matt-nel/UJ_Fluidic_backbone/CAD_files/syringe_pump/carriage.SLDPRT

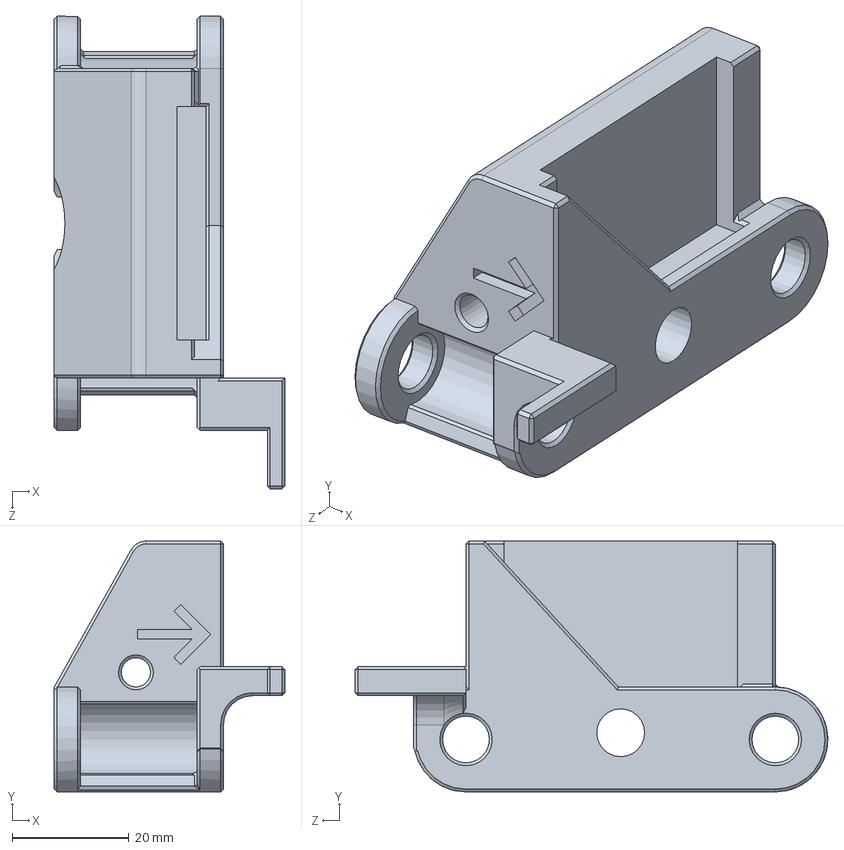
[picture p25: CAD file, 2021-12-11]
CAD_files/syringe_pump/carriage.SLDPRT
39.5 x 43.0 x 81.0 mm
