matt-nel/UJ_Fluidic_backbone/CAD_files/selector_valve/valve_gearbox_mount.SLDPRT

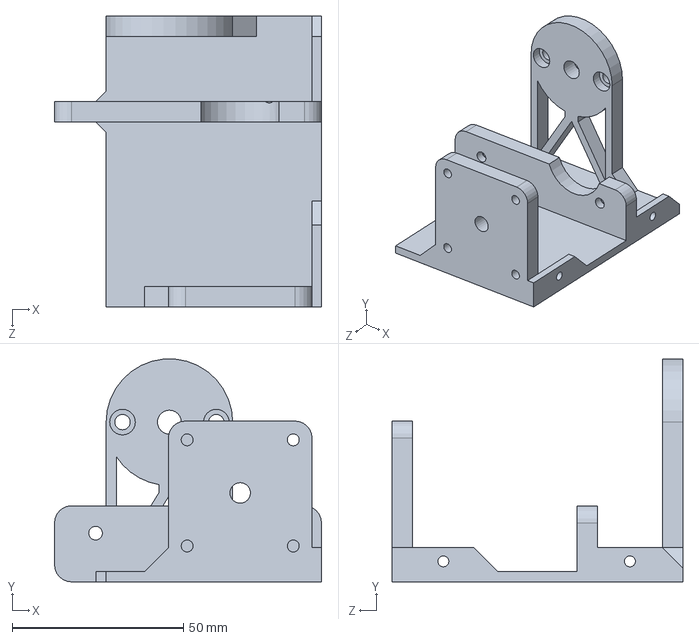
[picture p26: CAD file, 2021-12-11]
CAD_files/selector_valve/valve_gearbox_mount.SLDPRT
78.0 x 65.1 x 85.0 mm
