matt-nel/UJ_Fluidic_backbone/CAD_files/selector_valve/6mm rod.SLDPRT

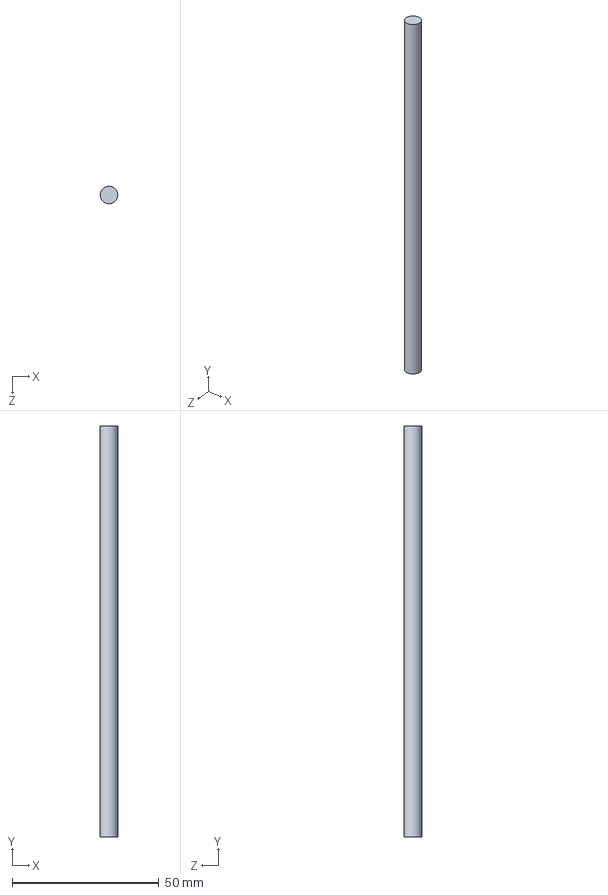
[picture p28: CAD file, 2021-12-11]
CAD_files/selector_valve/6mm rod.SLDPRT
6.00 x 140.0 x 6.00 mm
