matt-nel/UJ_Fluidic_backbone/CAD_files/syringe_pump/gap_sensor.SLDPRT

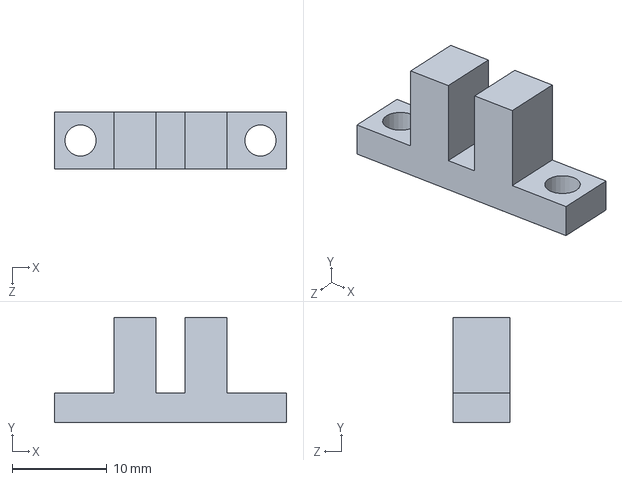
[picture p29: CAD file, 2021-12-11]
CAD_files/syringe_pump/gap_sensor.SLDPRT
24.5 x 11.1 x 6.00 mm
