matt-nel/UJ_Fluidic_backbone/CAD_files/reactor/reactor stand with fan.SLDPRT

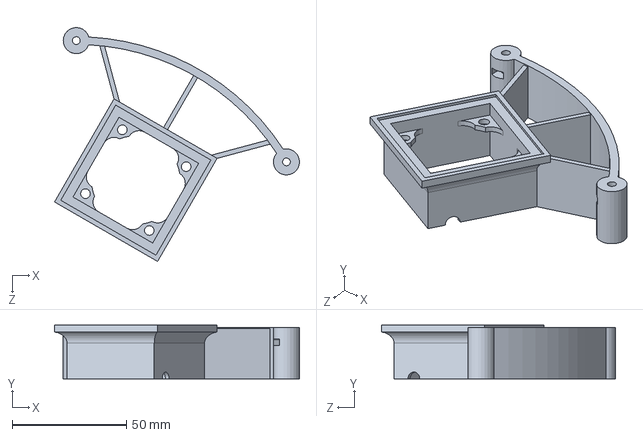
[picture p30: CAD file, 2021-12-11]
CAD_files/reactor/reactor stand with fan.SLDPRT
107.0 x 23.5 x 102.2 mm
