matt-nel/UJ_Fluidic_backbone/CAD_files/syringe_pump/endstop.SLDPRT

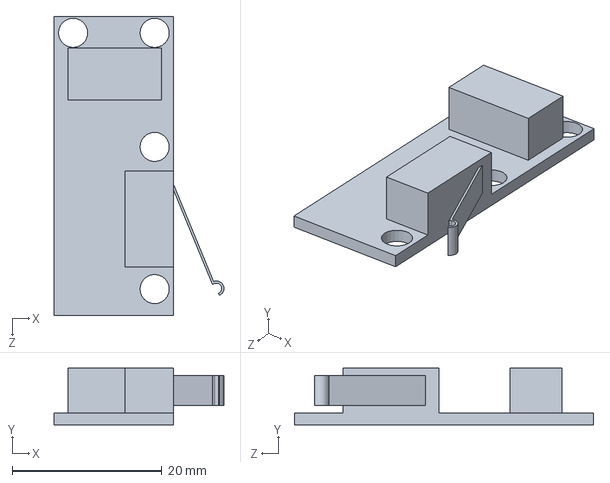
[picture p31: CAD file, 2021-12-11]
CAD_files/syringe_pump/endstop.SLDPRT
22.7 x 7.60 x 40.0 mm
