matt-nel/UJ_Fluidic_backbone/CAD_files/selector_valve/bearing.SLDPRT

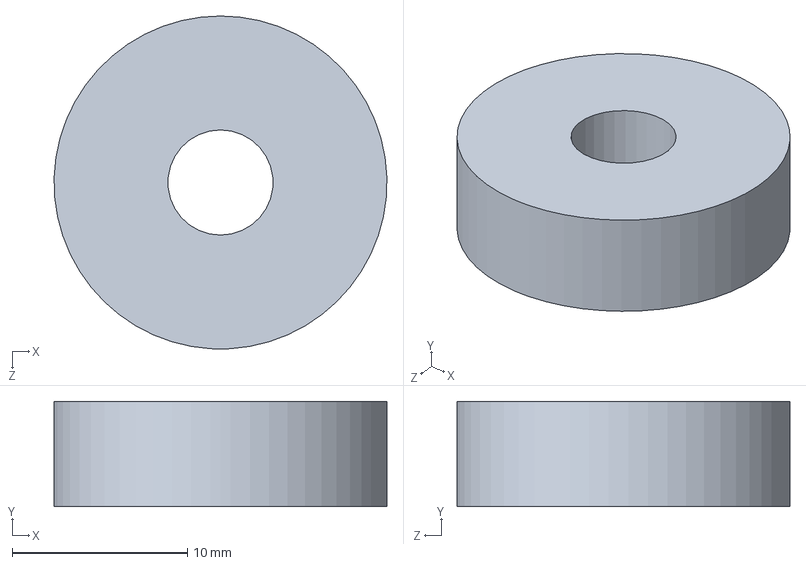
[picture p32: CAD file, 2021-12-11]
CAD_files/selector_valve/bearing.SLDPRT
19.0 x 6.00 x 19.0 mm
