matt-nel/UJ_Fluidic_backbone/CAD_files/syringe_pump/bottom adapter plate.SLDPRT

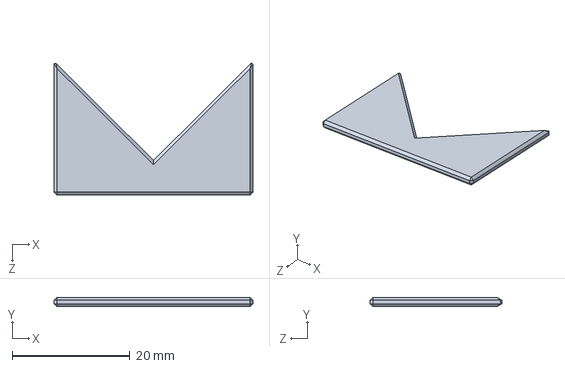
[picture p33: CAD file, 2021-12-11]
CAD_files/syringe_pump/bottom adapter plate.SLDPRT
33.8 x 1.60 x 22.5 mm
