matt-nel/UJ_Fluidic_backbone/CAD_files/reactor/n42 rect magnet.SLDPRT

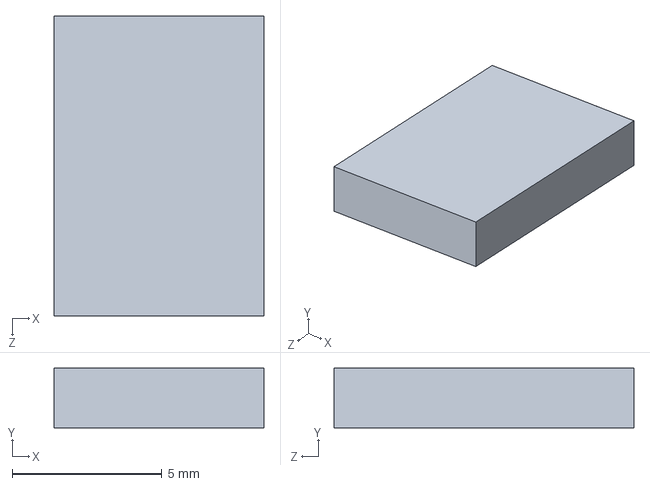
[picture p34: CAD file, 2021-12-11]
CAD_files/reactor/n42 rect magnet.SLDPRT
7.00 x 2.00 x 10.0 mm
