matt-nel/UJ_Fluidic_backbone/CAD_files/selector_valve/Driven gear 26T.SLDPRT

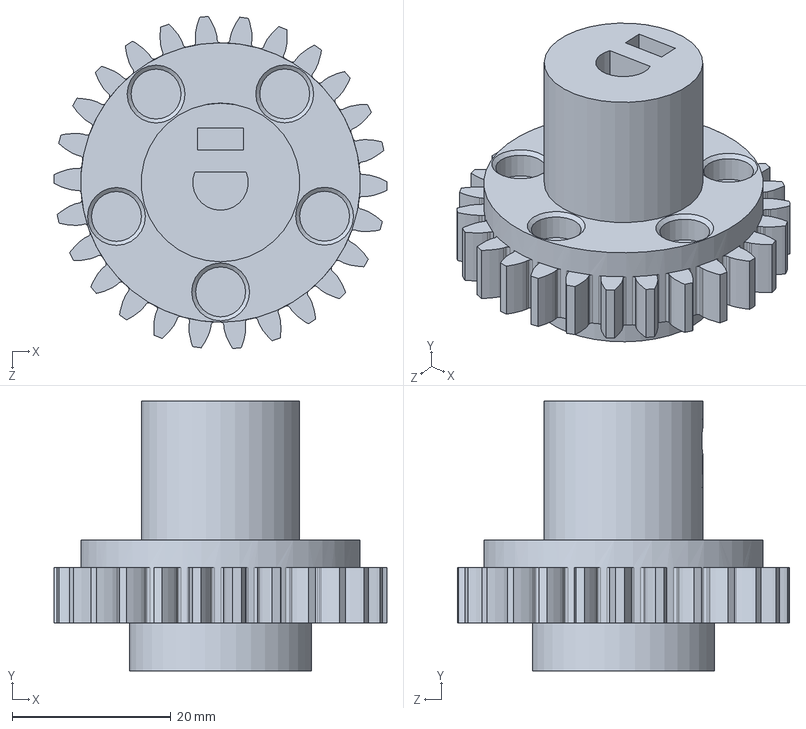
[picture p35: CAD file, 2021-12-11]
CAD_files/selector_valve/Driven gear 26T.SLDPRT
42.0 x 34.0 x 41.9 mm
