matt-nel/UJ_Fluidic_backbone/CAD_files/syringe_pump/carriage_v2.SLDPRT

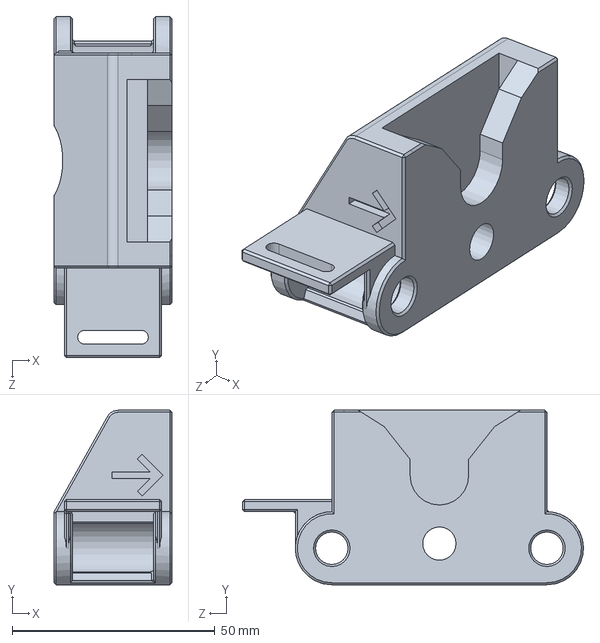
[picture p36: CAD file, 2021-12-11]
CAD_files/syringe_pump/carriage_v2.SLDPRT
29.0 x 43.0 x 84.0 mm
