matt-nel/UJ_Fluidic_backbone/CAD_files/selector_valve/grub.SLDPRT

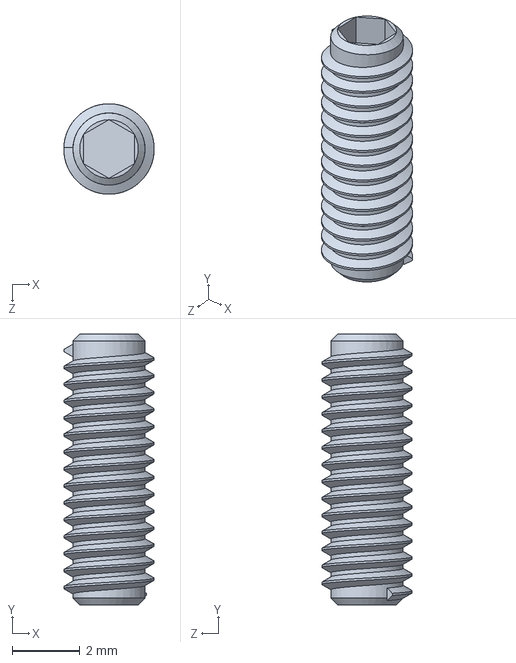
[picture p37: CAD file, 2021-12-11]
CAD_files/selector_valve/grub.SLDPRT
2.67 x 8.00 x 2.67 mm
