matt-nel/UJ_Fluidic_backbone/CAD_files/selector_valve/valve_gearbox_mount_vici.SLDPRT

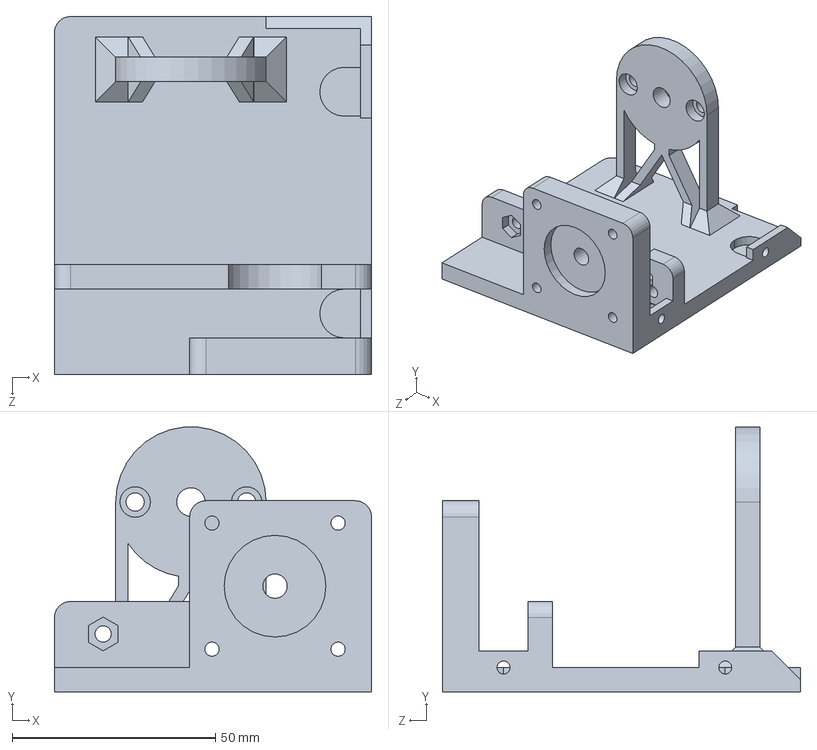
[picture p38: CAD file, 2021-12-11]
CAD_files/selector_valve/valve_gearbox_mount_vici.SLDPRT
78.0 x 65.1 x 88.0 mm
