matt-nel/UJ_Fluidic_backbone/CAD_files/syringe_pump/LM6UU.SLDPRT

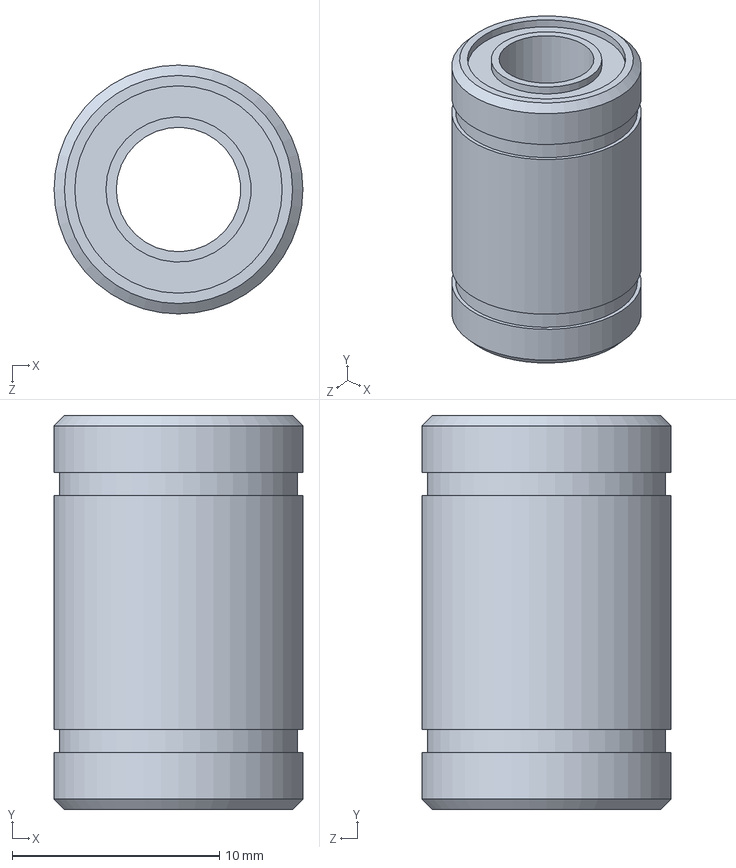
[picture p39: CAD file, 2021-12-11]
CAD_files/syringe_pump/LM6UU.SLDPRT
12.0 x 19.0 x 12.0 mm
