matt-nel/UJ_Fluidic_backbone/CAD_files/syringe_pump/syringe_holder.SLDPRT

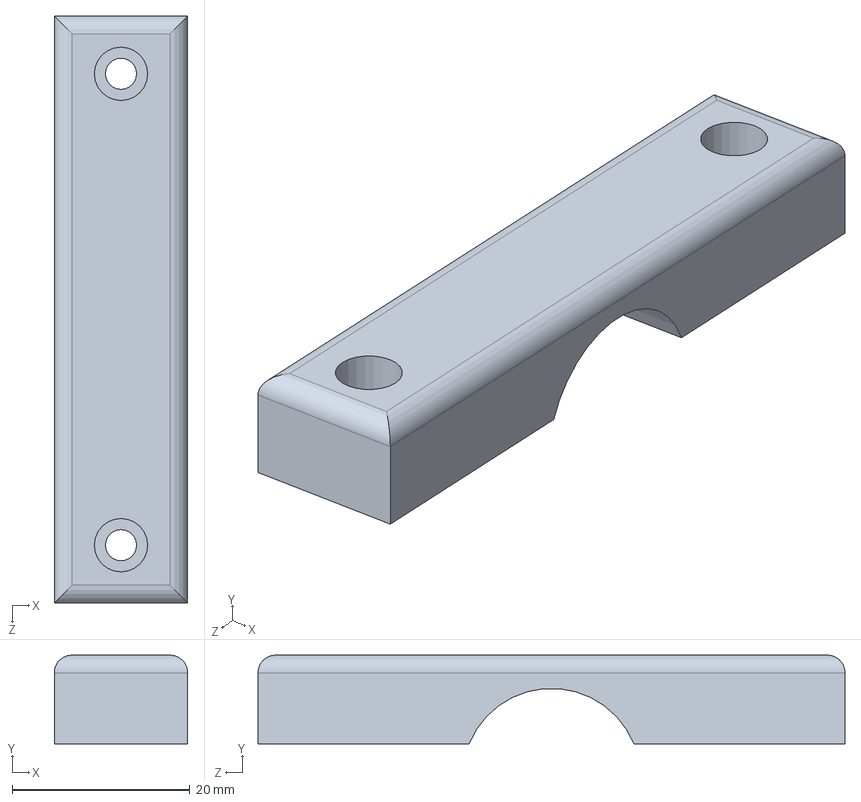
[picture p40: CAD file, 2021-12-11]
CAD_files/syringe_pump/syringe_holder.SLDPRT
15.0 x 10.0 x 66.0 mm
