matt-nel/UJ_Fluidic_backbone/CAD_files/syringe_pump/adjustable_endstop_arm.SLDPRT

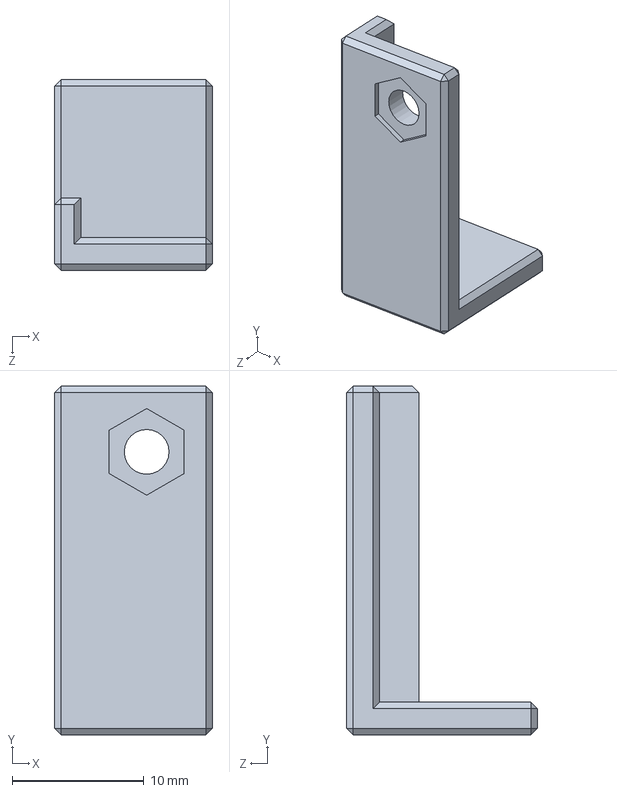
[picture p41: CAD file, 2021-12-11]
CAD_files/syringe_pump/adjustable_endstop_arm.SLDPRT
12.0 x 26.5 x 14.5 mm
