matt-nel/UJ_Fluidic_backbone/CAD_files/selector_valve/Driver gear 13T.SLDPRT

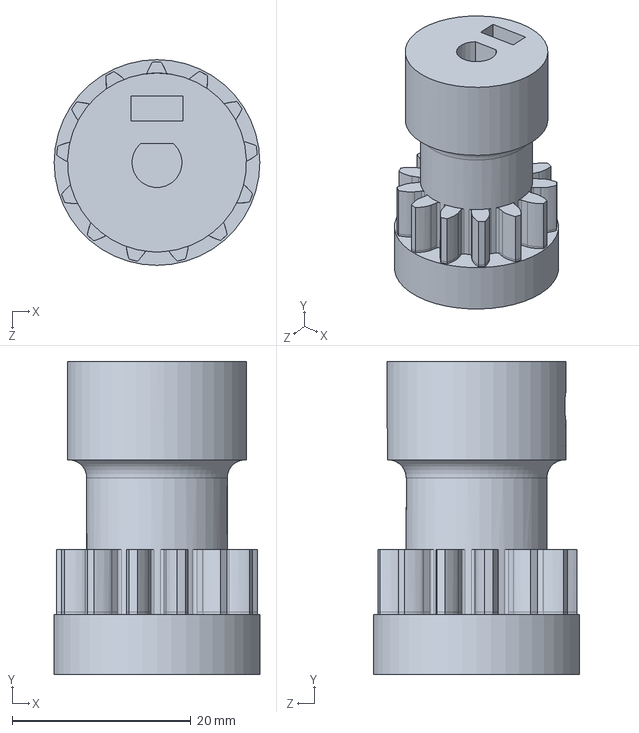
[picture p42: CAD file, 2021-12-11]
CAD_files/selector_valve/Driver gear 13T.SLDPRT
23.0 x 35.0 x 23.0 mm
