matt-nel/UJ_Fluidic_backbone/CAD_files/syringe_pump/slotted_wheel.SLDPRT

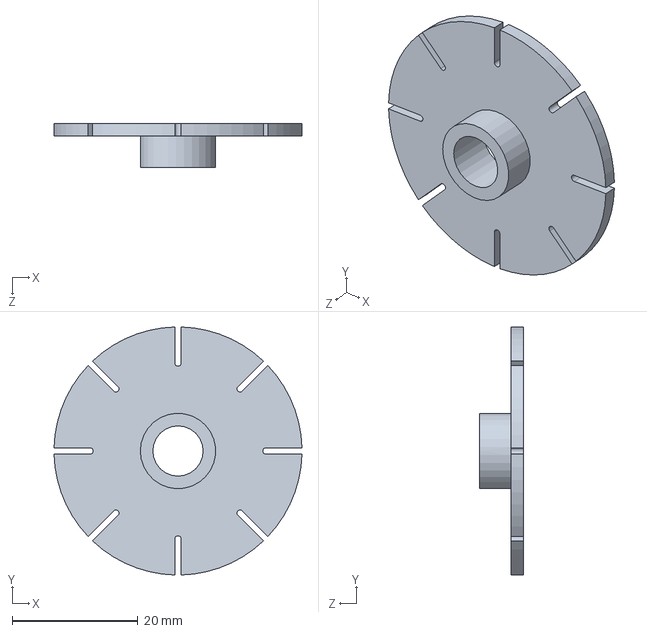
[picture p43: CAD file, 2021-12-11]
CAD_files/syringe_pump/slotted_wheel.SLDPRT
39.5 x 39.5 x 7.00 mm
