matt-nel/UJ_Fluidic_backbone/CAD_files/syringe_pump/endstop arm.SLDPRT

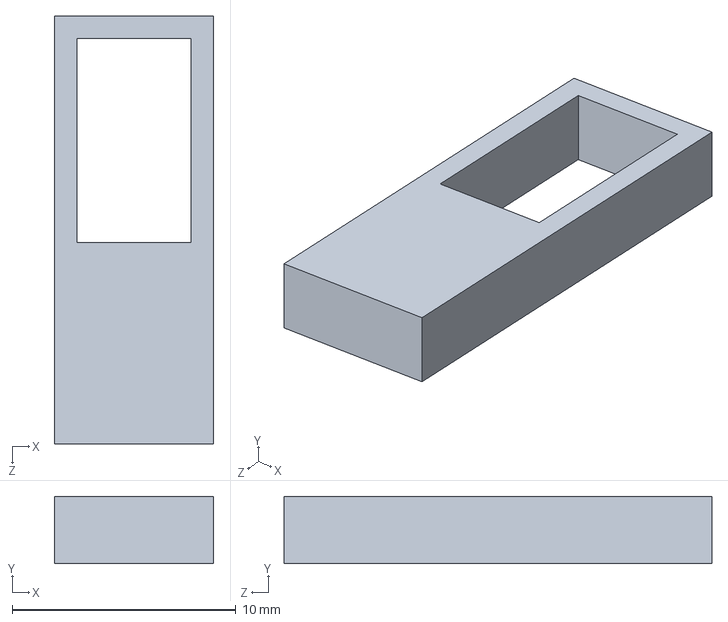
[picture p44: CAD file, 2021-12-11]
CAD_files/syringe_pump/endstop arm.SLDPRT
7.10 x 3.00 x 19.1 mm
