matt-nel/UJ_Fluidic_backbone/CAD_files/syringe_pump/Nema 17 Stepper Motor.SLDPRT

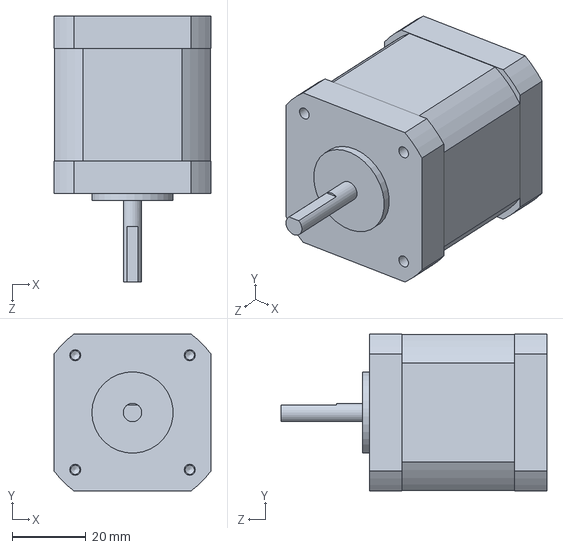
[picture p45: CAD file, 2021-12-11]
CAD_files/syringe_pump/Nema 17 Stepper Motor.SLDPRT
42.4 x 42.4 x 72.0 mm
