matt-nel/UJ_Fluidic_backbone/CAD_files/syringe_pump/syringe_adapter_bottom.SLDPRT

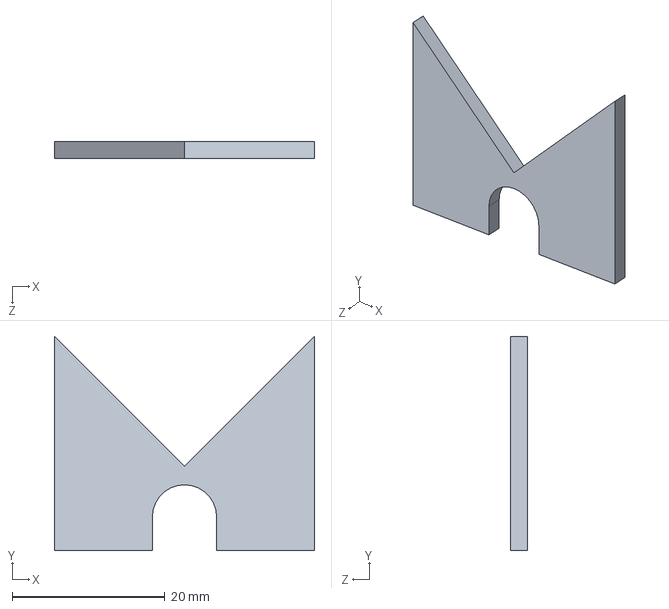
[picture p46: CAD file, 2021-12-11]
CAD_files/syringe_pump/syringe_adapter_bottom.SLDPRT
34.0 x 28.0 x 2.20 mm
