matt-nel/UJ_Fluidic_backbone/CAD_files/selector_valve/M4 x 35.SLDPRT

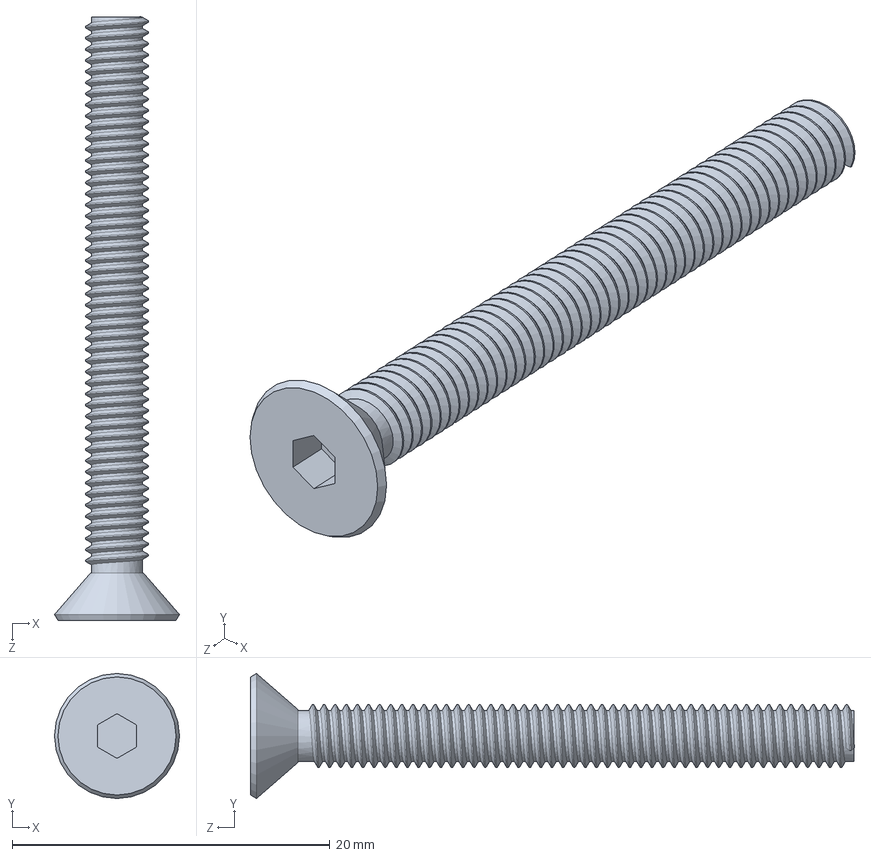
[picture p47: CAD file, 2021-12-11]
CAD_files/selector_valve/M4 x 35.SLDPRT
7.87 x 7.87 x 38.0 mm
