matt-nel/UJ_Fluidic_backbone/CAD_files/syringe_pump/tr8x8 115 mm.SLDPRT

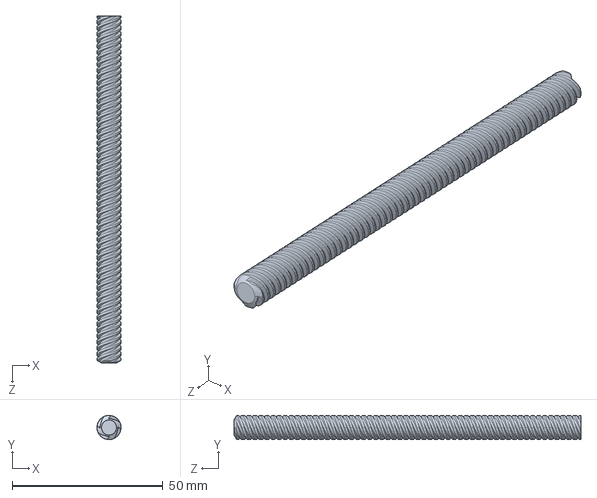
[picture p48: CAD file, 2021-12-11]
CAD_files/syringe_pump/tr8x8 115 mm.SLDPRT
8.00 x 8.00 x 115.0 mm
