matt-nel/UJ_Fluidic_backbone/CAD_files/selector_valve/8-32-8.SLDPRT

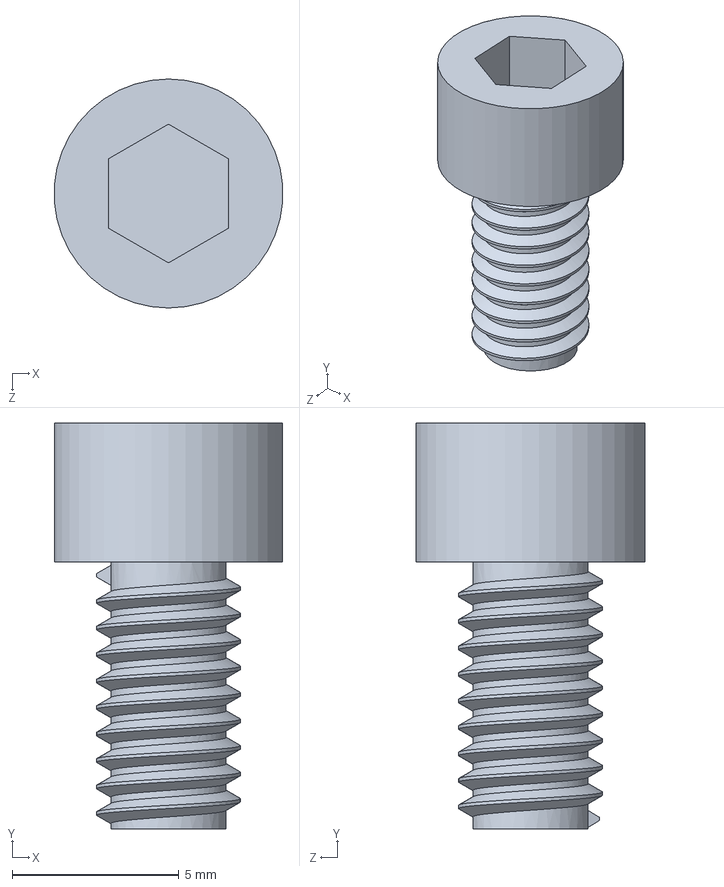
[picture p49: CAD file, 2021-12-11]
CAD_files/selector_valve/8-32-8.SLDPRT
6.84 x 12.2 x 6.86 mm
