matt-nel/UJ_Fluidic_backbone/CAD_files/selector_valve/Driven gear 25T.SLDPRT

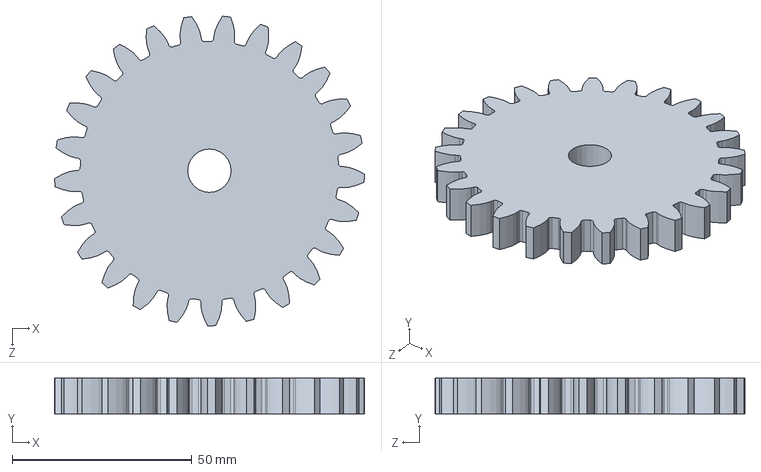
[picture p50: CAD file, 2021-12-11]
CAD_files/selector_valve/Driven gear 25T.SLDPRT
86.3 x 10.0 x 86.2 mm
