matt-nel/UJ_Fluidic_backbone/CAD_files/syringe_pump/adapter plate.SLDPRT

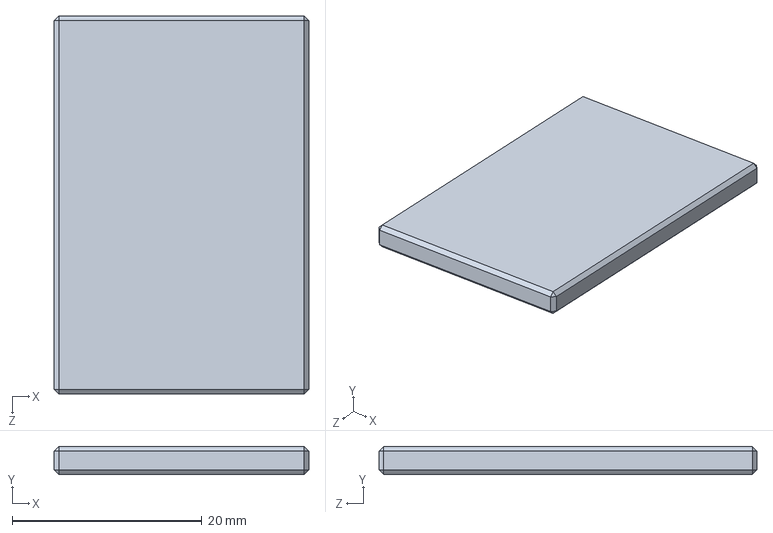
[picture p51: CAD file, 2021-12-11]
CAD_files/syringe_pump/adapter plate.SLDPRT
26.8 x 3.00 x 39.8 mm
