matt-nel/UJ_Fluidic_backbone/CAD_files/syringe_pump/Flexible Coupling 5mm x 8mm.SLDPRT

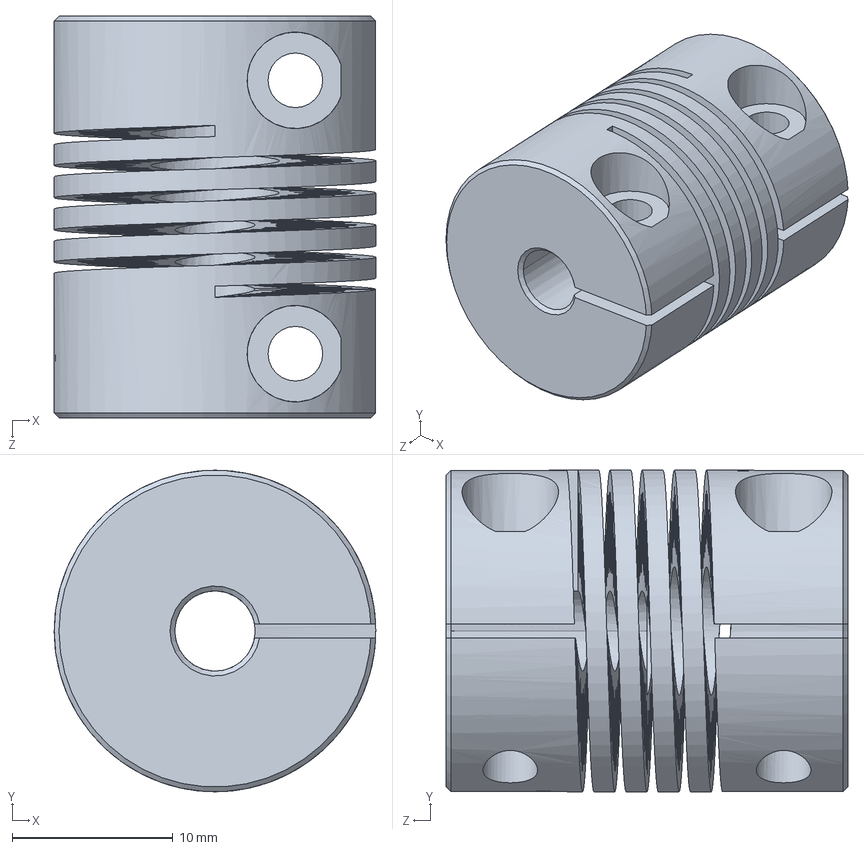
[picture p52: CAD file, 2021-12-11]
CAD_files/syringe_pump/Flexible Coupling 5mm x 8mm.SLDPRT
20.0 x 20.0 x 25.0 mm
