matt-nel/UJ_Fluidic_backbone/robot_setup.py

"""
 This script is used to start the setup program. The setup program will create the
 JSON files necessary to run the robot within the folder where the package has been
 installed on your system. 
"""

from UJ_FB import robot_setup

robot_setup()
