matt-nel/UJ_Fluidic_backbone/src/UJ_FB/setup_GUI.py

"""
This script contains the classes used to create JSON configuration files for the robot. 
Using this the SetupGUI, users can configure the robots graphically, without writing
JSON. This GUI assumes that the robot is run using an Arduino Mega 2560 and a RAMPS 1.4 
board. Most of the configuration information is temporarily held as a networkx graph. 
When the user generates the configuration files, the graph is encoded as a JSON file 
detailed the nodes and links (edges) of the graph. 
"""


import UJ_FB
import tkinter as tk
import os
import sys
import subprocess
import serial.tools.list_ports
import json
from PIL import ImageTk, Image
import cv2 as cv
import numpy as np
import networkx as nx

FIELD_NAMES = {"Maximum volume in ml": "max_volume",
               "Current volume in ml": "cur_volume",
               "Aluminium volume [m3] (eg. 1e-6)": "aluminium_volume",
               "Name": "name",
               "Fan speed RPM": "fan_speed",
               "Maximum samples": "max_samples",
               "Contents": "contents"
               }

UNITS = {"max_volume": "float",
         "cur_volume": "float",
         "fan_speed": "int",
         "max_samples": "int"}


def start_gui():
    root = tk.Tk()
    SetupGUI(root)
    root.mainloop()


def populate_ports():
    """
    Gets the serial ports available for connection
    :return: List of Arduinos available on the system
    """
    if sys.platform.startswith("win"):
        arduino_list = [port for port in serial.tools.list_ports.comports() if "arduino" in port.description.lower()]
    elif sys.platform.startswith("linux") or sys.platform.startswith("cygwin"):
        arduino_list = [port for port in serial.tools.list_ports.comports() if "acm" in port.description.lower()]
    else:
        raise EnvironmentError("Unsupported platform")

    return [name.name for name in arduino_list]


class CmdConfig:
    """Simple class to hold and generate the configuration for the CommandManager.
    """
    def __init__(self):
        self.ios = []
        self.devices = {}

    def load_existing(self, ios, devices):
        self.ios = ios
        self.devices = devices

    def as_dict(self):
        return {"ios": self.ios, "devices": self.devices}


class SetupGUI:
    """Class used to run the GUI. 
    """
    def __init__(self, primary):
        # Setup initialisation
        self.primary = primary
        self.primary.title("Fluidic backbone setup")
        self.primary.configure(background="#FFFFFF")

        script_dir = os.path.abspath(UJ_FB.__file__)
        script_dir = script_dir.split("\\")
        self.script_dir = "\\".join(script_dir[:-1])
        if not os.path.exists(os.path.join(self.script_dir, "configs")):
            os.chdir(self.script_dir)
            os.mkdir("configs")
        self.config_filenames = ["cmd_config.json", "module_connections.json", "running_config.json"]
        self.default_configs = ["default_configs/single_valve/", "default_configs/single_valve_reactor/",
                                "default_configs/two_valve_reactor/", "configs/"]

        self.frame = np.array([])
        self.fonts = {"buttons": ("Comic Sans MS", 12), "labels": ("Comic Sans MS", 14),
                      "default": ("Comic Sans MS", 16),
                      "heading": ("Comic Sans MS", 16), "text": ("Comic Sans MS", 12)}
        self.colours = {"accept-button": "#4de60b", "cancel-button": "#e6250b",
                        "heading": "#e65525", "other-button": "#45296e", "other-button-text": "#FFFFFF",
                        "form-bg": "#b5d5ff", "form-bg2": "#377bd4"}
        image_dir = os.path.join(self.script_dir, "valve.png")
        self.valve_image = ImageTk.PhotoImage(Image.open(image_dir))
        self.text_temp = ""
        self.int_temp = 0
        self.config_cmd_flag = False
        self.config_cxn_flag = False
        self.exit_flag = False

        # Robot parameters
        self.key = ""
        self.id = ""
        self.rxn_name = ""
        self.roi = []
        self.used_motor_connectors = {}
        self.used_endstop_connectors = {}
        self.used_he_pins = []
        self.used_valves = []
        self.com_ports = []

        self.modules = {}
        self.graph = nx.MultiGraph()
        self.graph_tmp = nx.MultiGraph()
        self.node_config = None
        self.num_syringes = 0
        self.num_valves = 0
        self.conf_syr = 0
        self.conf_valves = 0
        self.conf_storage = 0
        self.num_he_sens = 0
        self.num_flasks = 0
        self.num_reactors = 0
        self.valves_buttons = {}
        self.simulation = False
        self.cmd_devices = CmdConfig()
        self.default_running_config = {
            "url": "http://127.0.0.1:5000/robots_api",
            "magnet_readings": {"valve1": {"1": 0, "3": 0, "5": 0, "7": 0, "9": 0}, "valve2": {"1": 0, "3": 0,
                                                                                               "5": 0, "7": 0, "9": 0},
                                "check_magnets": 0},
            "valve_backlash": {"valve1": {"check_backlash": 0, "backlash_steps": 0},
                               "valve2": {"check_backlash": 0, "backlash_steps": 0}},
            "valve_pos": {"valve1": None, "valve2": None}}

        self.es_options = {"X min": 3, "X max": 2, "Y min": 14, "Y max": 15, "Z min": 18, "Z max": 19}
        self.motor_configs = {"default": {"steps_per_rev": 3200, "enabled_acceleration": False, "speed": 1000,
                                          "max_speed": 10000, "acceleration": 1000},
                              "cmd_default": {"enabled_acceleration": False, "speed": 1000, "max_speed": 10000,
                                              "acceleration": 1000},
                              "valve": {"steps_per_rev": 3200, "enabled_acceleration": False, "speed": 1000,
                                        "max_speed": 4000, "acceleration": 1000}
                              }
        self.motor_options = {"X": {"stepperX": {"cmd_id": "STPX",
                                                 "device_config": {}}},
                              "Y": {"stepperY": {"cmd_id": "STPY",
                                                 "device_config": {}}},
                              "Z": {"stepperZ": {"cmd_id": "STPZ",
                                                 "device_config": {}}},
                              "E0": {"stepperE0": {"cmd_id": "STPE0",
                                                   "device_config": {}}},
                              "E1": {"stepperE1": {"cmd_id": "STPE1",
                                                   "device_config": {}}}}

        steppers = [("stepperX", "STPX"), ("stepperY", "STPY"), ("stepperZ", "STPZ"),
                    ("stepperE0", "STPE0"), ("stepperE1", "STPE1")]
        for stepper in steppers:
            self.cmd_devices.devices[stepper[0]] = {"command_id": stepper[1],
                                                    "config": self.motor_configs["default"]}

        # Setup UI
        self.setup_frame = tk.Frame(self.primary, bg=self.colours["form-bg"], borderwidth=5)
        self.utilities_frame = tk.Frame(self.primary, bg=self.colours["form-bg"], borderwidth=2, height=40)
        self.log_frame = tk.Frame(self.primary)
        self.log = tk.Text(self.log_frame, state="disable", width=80, height=8, wrap="none", borderwidth=5)

        self.setup_label = tk.Label(self.primary, text="Fluidic backbone setup:", font=self.fonts["heading"],
                                    fg=self.colours["heading"], bg="#FFFFFF",
                                    padx=2)
        self.utilities_label = tk.Label(self.primary, text="Utilities", font=self.fonts["heading"], padx=2,
                                        bg="#ffffff", fg=self.colours["heading"])

        self.log_frame.grid(row=4, column=2, padx=5, pady=10)
        self.log.grid(row=0, column=0)
        self.setup_label.grid(row=2, column=2)
        self.utilities_label.grid(row=2, column=10)
        self.setup_frame.grid(row=3, column=2)
        self.utilities_frame.grid(row=3, column=10)

        self.init_setup_panel()
        self.init_utilities_panel()

    def init_setup_panel(self):
        """Starts the setup frame, which is the main part of the initial window. Using this frame,
        user can configure the serial port, robot id, robot key, reaction name, and module information.
        """
        def display_ports(ports, refresh=False):
            i = 0
            if ports:
                label = tk.Label(com_frame, text="Available ports:", font=self.fonts["heading"],
                                 bg=self.colours["form-bg"], fg=self.colours["heading"])
                label.grid(row=2, columnspan=2)
                for name in ports:
                    c_port_button = tk.Button(com_frame, text="Arduino on " + name, font=button_font,
                                              bg=self.colours["other-button"],
                                              fg=self.colours["other-button-text"], width=20,
                                              command=lambda: add_com_port(name))
                    c_port_button.grid(row=3, column=i)
                    i += 1
            else:
                ports = populate_ports()
                if ports and refresh:
                    display_ports(ports)
                else:
                    no_ports = tk.Label(com_frame, text="No ports available, click refresh or use the text box",
                                        font=self.fonts["labels"], bg="gray", fg=self.colours["other-button-text"],)
                    no_ports.grid(row=3, column=i)

        def add_com_port(port_name=""):
            if port_name == "":
                port = self.text_temp
                self.cmd_devices.ios.append({"port": port})
                self.write_message(f"Port {port} added")
                com_port_entry.delete(0, "end")
            else:
                if "tty" in port_name:
                    port_name = "/dev/" + port_name
                self.cmd_devices.ios.append({"port": port_name})
                self.write_message(f"Port {port_name} added")

        def add_key():
            self.key = self.text_temp
            robot_key_entry.delete(0, "end")
            self.write_message(f"Robot key added")

        def add_id():
            self.id = self.text_temp
            robot_id_entry.delete(0, "end")
            self.write_message(f"Robot ID added")

        def add_rxn_name():
            self.rxn_name = reaction_name_entry.get()
            reaction_name_entry.delete(0, "end")
            self.write_message(f"Reaction name {self.rxn_name} added")

        button_font = self.fonts["buttons"]
        com_frame = tk.Frame(self.setup_frame, bg=self.colours["form-bg2"], pady=4)
        com_frame.grid(row=2)

        com_port_label = tk.Label(self.setup_frame, text="Choose an arduino to connect to by clicking the button,\n"
                                                         "or write the name of the "
                                                         "com port in the text box and click accept:",
                                  font=self.fonts["labels"], fg=self.colours["heading"], bg=self.colours["form-bg"],)
        com_port_label.grid(row=1, column=0)
        avail_ports = populate_ports()
        refresh_button = tk.Button(com_frame, text="Refresh", font=button_font, bg="LemonChiffon2",
                                   fg="black", command=lambda: display_ports(avail_ports, refresh=True), width=15)
        refresh_button.grid(row=3, column=2)
        display_ports(avail_ports)

        val_text = self.primary.register(self.validate_text)
        cp_entry_label = tk.Label(com_frame, text="Please enter the COM port: ", bg=self.colours["form-bg"],
                                  font=self.fonts["labels"], fg=self.colours["heading"], width=25)
        com_port_entry = tk.Entry(com_frame, validate="key", validatecommand=(val_text, "%P"),
                                  bg="#FFFFFF", fg="black", width=15)
        com_port_button = tk.Button(com_frame, text="Accept port", font=self.fonts["buttons"], bg="lawn green",
                                    fg="black", command=add_com_port, width=15)

        cp_entry_label.grid(row=4, column=0, padx=4)
        com_port_entry.grid(row=4, column=1, padx=4)
        com_port_button.grid(row=4, column=2, padx=4)

        robot_id_label = tk.Label(com_frame, text="Please enter the robot ID: ", bg=self.colours["form-bg"],
                                  font=self.fonts["labels"], fg=self.colours["heading"], width=25)
        robot_id_entry = tk.Entry(com_frame, validate="key", validatecommand=(val_text, "%P"), bg="#FFFFFF", fg="black",
                                  width=15)
        robot_id_button = tk.Button(com_frame, text="Accept ID", font=button_font, bg="lawn green", fg="black",
                                    command=add_id, width=15)

        robot_key_label = tk.Label(com_frame, text="Please enter the robot key: ", font=self.fonts["labels"],
                                   bg=self.colours["form-bg"], fg=self.colours["heading"], width=25)
        robot_key_entry = tk.Entry(com_frame, validate="key", validatecommand=(val_text, "%P"), bg="#FFFFFF",
                                   fg="black", width=15)
        robot_key_button = tk.Button(com_frame, text="Accept key", font=button_font, bg="lawn green", fg="black",
                                     command=add_key, width=15)
        reaction_name_label = tk.Label(com_frame, text="Please enter reaction name: ", font=self.fonts["labels"],
                                       bg=self.colours["form-bg"], fg=self.colours["heading"], width=25)
        reaction_name_butt = tk.Button(com_frame, text="Accept name", font=self.fonts["buttons"],
                                       bg="lawn green", command=add_rxn_name, width=15)
        reaction_name_entry = tk.Entry(com_frame, width=15)

        robot_id_label.grid(row=5, column=0, padx=4)
        robot_id_entry.grid(row=5, column=1, padx=4)
        robot_id_button.grid(row=5, column=2, padx=4)
        robot_key_label.grid(row=6, column=0, padx=4)
        robot_key_entry.grid(row=6, column=1, padx=4)
        robot_key_button.grid(row=6, column=2, padx=4)
        reaction_name_label.grid(row=7, column=0, padx=4)
        reaction_name_entry.grid(row=7, column=1, padx=4)
        reaction_name_butt.grid(row=7, column=2, padx=4)

        mod_frame = tk.Frame(self.setup_frame, bg=self.colours["form-bg"])
        mod_label = tk.Label(mod_frame, text="Backbone modules and connections setup:", font=self.fonts["labels"],
                             bg=self.colours["form-bg"], fg=self.colours["heading"])
        mod_button = tk.Button(mod_frame, text="Configure modules", font=button_font, bg=self.colours["other-button"],
                               fg=self.colours["other-button-text"], command=self.graph_setup, width=20)

        mod_frame.grid(row=3)
        mod_label.grid(row=1, column=0, padx=60)
        mod_button.grid(row=1, column=2, pady=4)

    def init_utilities_panel(self):
        """Contains the buttons used to load existing configuration files, clear the current configuration,
        or start the robot as a subprocess.
        """
        but_width = 25
        button_font = self.fonts["buttons"]
        run_fb_button = tk.Button(self.utilities_frame, text="Run Fluidic Backbone", font=self.fonts["buttons"],
                                  bg="DeepSkyBlue", fg="black", command=self.run_fb_menu, width=but_width, padx=2)
        lc_butt = tk.Button(self.utilities_frame, text="Load existing configuration", font=button_font,
                            bg=self.colours["other-button"], fg=self.colours["other-button-text"],
                            command=self.load_configs, width=but_width, padx=2)
        cc_butt = tk.Button(self.utilities_frame, text="Clear configuration", font=self.fonts["buttons"],
                            bg="Tomato2", fg="black", command=self.clear_configs, width=but_width, padx=2)
        dc_butt = tk.Button(self.utilities_frame, text="Load a default configuration", font=self.fonts["buttons"],
                            bg=self.colours["other-button"], fg=self.colours["other-button-text"],
                            command=self.load_default_config, width=but_width, padx=2)
        gen_button = tk.Button(self.utilities_frame, text="Save configuration", font=button_font, bg="lawn green",
                               fg="black", command=self.generate_config, width=but_width, padx=2)

        lc_butt.grid(row=1, column=0, padx=4, pady=4)
        dc_butt.grid(row=2, column=0, padx=4, pady=4)
        gen_button.grid(row=3, padx=4, pady=4)
        cc_butt.grid(row=4, column=0, padx=4, pady=4)
        run_fb_button.grid(row=5, column=0, padx=4, pady=10)

    def graph_setup(self):
        """This function is used to set up the graph for the robot. The networkx graph contains all the information 
        required by the Fluidic Backbone to set up and control the modules. 
        """
        def accept():
            if self.conf_valves > 0 and self.conf_syr > 0:
                self.config_cxn_flags = True
                self.config_cmd_flag = True
                self.graph = self.graph_tmp
                graph_setup.destroy()
            else:
                self.write_message("Required to configure at least one valve and syringe")

        def reset_graph_setup():
            self.modules = {}
            graph_setup.destroy()

        def populate_menus(frame, valve_no, row_count, port, col, pad=2, span=False):
            """Populates the buttons and option menus that surround each valve. Creates a frame to house
            each button and menu.

            Args:
                frame (tk.Frame): the frame that this button is a child of
                valve_no (int): the number of the valve this module is being configured for.
                row_count (int): the current row number to align the frame to 
                port (int): the valve port connected to this module
                col (int): the column to align the frame to
                pad (int, optional): the amount of padding around the frame. Defaults to 2.
                span (bool, optional): whether the frame should span 2. Defaults to False.
            """
            new_frame = tk.Frame(frame)
            col_span = 1
            if span:
                col_span = 2
            row = row_count * 2
            new_frame.grid(row=row, column=col, columnspan=col_span, pady=pad)
            module_type = tk.StringVar(new_frame)
            module_type.set("")
            port_button = tk.Button(new_frame, text=f"Configure port {port}", bg="LightBlue3", fg="black", width=15,
                                    font=self.fonts["buttons"])
            port_button.grid(row=1, column=1)
            port_om = tk.OptionMenu(new_frame, module_type, *module_options)
            port_om.grid(row=2, column=1)
            port_button.configure(command=lambda v=valve_no,
                                  mt=module_type, p=port, pb=port_button: port_menu_start(v, mt, p, pb))
            self.valves_buttons[valve_name][port] = port_button
            node = self.get_node(valve_name, port)
            if node:
                port_button.configure(bg="lawn green")
                module_type.set(self.graph_tmp.nodes[node]["mod_type"])

        def port_menu_start(valve_no, module_type, port_no, button):
            """Starts the popup window to configure the module attached to that port. Modules can be reconfigured
            later by clicking on the button again.

            Args:
                valve_no (int): the number of the valve that this module is connected to.
                module_type (tk.StringVar): what type of module is connected to this port.
                port_no (int): the port number (1-10) that this module is connected to
                button (tk.Button): the button used to start this menu
            """
            this_module_type = module_type.get()
            if this_module_type != "":
                port_options_window = tk.Toplevel(self.primary)
                this_valve_name = f"valve{valve_no + 1}"
                # Hold the information about this valve
                valve_info = {"valve_name": this_valve_name, "valve_id": valve_no, "port_no": port_no}
                # Hold known information about the node, used to configure a node on the graph within the 
                # popup window.
                node_info = {"entries": []}
                title = tk.Label(port_options_window, text=f"Configure port {port_no} on {this_valve_name}",
                                 font=self.fonts["heading"], fg=self.colours["heading"])
                title.grid(row=0, column=0, columnspan=2)
                type_label = tk.Label(port_options_window, text=this_module_type.capitalize(),
                                      font=self.fonts["heading"], fg=self.colours["heading"])
                type_label.grid(row=1, column=0, columnspan=2)
                found_node = self.get_node(this_valve_name, port_no)
                # Depending on which module type we are configuring, start a different setup window.
                if this_module_type == "flask":
                    node_info["mod_type"] = "flask"
                    node_info["class_type"] = "FBFlask"
                    fields = ["Current volume in ml", "Maximum volume in ml", "Contents",
                              "Tubing length in mm"]
                    self.flask_setup(node_info, valve_info, fields, port_options_window, button, found_node)
                elif this_module_type == "reactor":
                    node_info["mod_type"] = "reactor"
                    node_info["class_type"] = "Reactor"
                    fields = ["Current volume in ml", "Maximum volume in ml",
                              "Contents", "Fan speed RPM", "Aluminium volume [m3] (eg. 1e-6)", "Tubing length in mm"]
                    self.reactor_setup(node_info, valve_info, fields, port_options_window, button, found_node)
                elif this_module_type == "syringe_pump":
                    node_info["mod_type"] = "syringe_pump"
                    node_info["class_type"] = "SyringePump"
                    fields = ["Current volume in ml", "Maximum volume in ml", "Contents"]
                    fields.pop(0)
                    self.syringe_setup(node_info, valve_info, fields, port_options_window, button, found_node)
                elif this_module_type == "selector_valve":
                    fields = ["Tubing length in mm"]
                    self.valve_link(node_info, valve_info, fields, port_options_window, button, found_node)
                elif this_module_type == "waste":
                    node_info["mod_type"] = "waste"
                    node_info["class_type"] = "FBFlask"
                    node_info["Contents"] = "Waste"
                    fields = ["Current volume in ml", "Maximum volume in ml", "Tubing length in mm"]
                    self.flask_setup(node_info, valve_info, fields, port_options_window, button, found_node)
                elif this_module_type == "filter":
                    node_info["mod_type"] = "filter"
                    node_info["class_type"] = "FBFlask"
                    fields = ["Current volume in ml", "Maximum volume in ml", "Dead volume in ml"]
                    self.flask_setup(node_info, valve_info, fields, port_options_window, button, found_node)
                elif this_module_type == "storage":
                    node_info["mod_type"] = "storage"
                    node_info["class_type"] = "FluidStorage"
                    fields = ["Maximum volume in ml", "Tubing length in mm", "Maximum samples"]
                    self.storage_setup(node_info, valve_info, fields, port_options_window, button, found_node)

        # Ask the user how many valves and syringes are connected to this particular setup. 
        if self.num_valves == 0 or self.num_syringes == 0:
            if self.num_valves == 0:
                valves_query = tk.Toplevel(self.primary)
                valves_query.attributes("-topmost", "true")
                q_label = tk.Label(valves_query, text="How many valves are attached to the backbone?",
                                   font=self.fonts["heading"], fg=self.colours["heading"])
                validate_valves = valves_query.register(self.validate_int)
                q_entry = tk.Entry(valves_query, validate="key", validatecommand=(validate_valves, "%P"))
                ok_button = tk.Button(valves_query, text="Accept", bg="lawn green", font=self.fonts["buttons"],
                                      command=lambda: self.add_mod("selector_valve", valves_query))
                cancel_button = tk.Button(valves_query, text="Cancel", bg="tomato2", font=self.fonts["buttons"],
                                          command=valves_query.destroy)

                q_label.grid(row=0, column=1)
                q_entry.grid(row=1, column=1)
                ok_button.grid(row=2, column=2)
                cancel_button.grid(row=2, column=3)

            if self.num_syringes == 0:
                syringe_query = tk.Toplevel(self.primary)
                syringe_query.attributes("-topmost", "true")
                q_label = tk.Label(syringe_query, text="How many syringes are attached to the backbone?",
                                   font=self.fonts["heading"], fg=self.colours["heading"])
                validate_syr = syringe_query.register(self.validate_int)
                q_entry = tk.Entry(syringe_query, validate="key", validatecommand=(validate_syr, "%P"))
                ok_button = tk.Button(syringe_query, text="Accept", bg="lawn green", font=self.fonts["buttons"],
                                      command=lambda: self.add_mod("syringe_pump", syringe_query))
                cancel_button = tk.Button(syringe_query, text="Cancel", bg="tomato2",
                                          font=self.fonts["buttons"], command=syringe_query.destroy)

                q_label.grid(row=0, column=1)
                q_entry.grid(row=1, column=1)
                ok_button.grid(row=2, column=2)
                cancel_button.grid(row=2, column=3)
        # Create the popup window, arraying configuration buttons around each valve.
        else:
            graph_setup = tk.Toplevel(self.primary)
            graph_setup.title("Backbone connections setup")
            graph_setup.configure(bg="#ffffff")
            module_options = ["filter", "flask", "reactor", "storage", "syringe_pump", "selector_valve", "waste", ]
            for i in range(0, self.num_valves):
                valve_frame = tk.Frame(graph_setup)
                left_ports = tk.Frame(valve_frame)
                img_frame = tk.Frame(valve_frame)
                right_ports = tk.Frame(valve_frame)
                valve_name = f"valve{i + 1}"
                self.valves_buttons[valve_name] = {-1: None, 1: None, 2: None, 3: None, 4: None, 5: None, 6: None,
                                                   7: None, 8: None, 9: None, 10: None, "cfg": None}
                if not self.config_cxn_flag:
                    self.graph_tmp.add_node(valve_name)
                    self.graph_tmp.nodes[valve_name]["name"] = valve_name
                    self.graph_tmp.nodes[valve_name]["mod_type"] = "selector_valve"
                    self.graph_tmp.nodes[valve_name]["class_type"] = "SelectorValve"
                top_label = tk.Label(valve_frame, text=f"Valve {i + 1}", font=self.fonts["heading"],
                                     fg=self.colours["heading"])

                top_label.grid(row=0, column=1)
                valve_frame.grid(row=1, column=i, padx=10)
                img_frame.grid(row=1, column=1)
                left_ports.grid(row=1, column=0)
                right_ports.grid(row=1, column=2)

                for j, k in enumerate(range(2, 6)):
                    populate_menus(left_ports, valve_no=i, row_count=j, port=k, pad=5, col=0)

                image = tk.Label(img_frame, image=self.valve_image)
                image.grid(row=3, column=0, columnspan=2)
                populate_menus(img_frame, valve_no=i, row_count=0, port=1, col=0)
                populate_menus(img_frame, valve_no=i, row_count=0, port=-1, col=1)
                populate_menus(img_frame, valve_no=i, row_count=3, port=6, col=0, span=True)

                for j, k in enumerate(range(10, 6, -1)):
                    populate_menus(right_ports, valve_no=i, row_count=j, port=k, pad=5, col=2)

                self.valves_buttons[valve_name]["cfg"] = tk.Button(img_frame, text=f"Valve {i + 1} setup",
                                                                   font=self.fonts["buttons"], bg="LightBlue3",
                                                                   fg="black")
                self.valves_buttons[valve_name]["cfg"].grid(row=9, column=0, columnspan=2)
                self.valves_buttons[valve_name]["cfg"].configure(
                    command=lambda vn=valve_name, valve_butt=self.valves_buttons[valve_name]["cfg"]:
                    self.valve_setup({"valve_name": vn}, valve_butt))
                if self.graph_tmp.nodes[valve_name].get("mod_config"):
                    self.valves_buttons[valve_name]["cfg"].configure(bg="lawn green")
            camera_butt = tk.Button(graph_setup, text="Set up camera", bg=self.colours["other-button"], fg="white")
            camera_butt.configure(command=lambda: self.camera_setup(camera_butt))
            accept_butt = tk.Button(graph_setup, text="Accept", bg="lawn green", command=accept,
                                    font=self.fonts["buttons"])
            cancel_butt = tk.Button(graph_setup, text="Cancel", bg="tomato2", font=self.fonts["buttons"],
                                    command=reset_graph_setup)
            camera_butt.grid(row=2, column=0)
            accept_butt.grid(row=3, column=1)
            cancel_butt.grid(row=3, column=2)

    def add_mod(self, mod_type, popup):
        """Adds new valves and syringe pumps to configure.

        Args:
            mod_type (str): the module type to be added.
            popup (tk.TopLevel): the popup window 
        """
        if mod_type == "syringe_pump":
            self.num_syringes = self.int_temp
        elif mod_type == "selector_valve":
            self.num_valves = self.int_temp
        popup.destroy()
        if self.num_syringes > 0 and self.num_valves > 0:
            self.graph_setup()

    def syringe_setup(self, node_info, valve_info, fields, window, button, found_node):
        """Starts a window for the user to configure the syringe. Syringes are generally connected to the middle port
        of the selector valve. Sets up the syringe using the information provided by the user 

        Args:
            node_info (dict): contains the known information about the node, like the module type. Also used to house
            the entries
            valve_info (dict): contains information about the valve this module is attached to
            fields (list): a list of input fields that the user should fill in to configure this module
            window (tk.TopLevel): the window created to configure the syringe
            button (tk.Button): the button used to start this window
            found_node (str): if a node has already been configured, this will be its name. Otherwise this is empty
        """
        def accept():
            motor_cxn = motor_connector.get()
            endstop = endstop_connector.get()
            select_new = False
            if motor_cxn and endstop:
                if motor_cxn in self.used_motor_connectors.keys() and not found_node:
                    select_new = True
                    self.write_message(
                        f"That motor connector is already used by {self.used_motor_connectors[motor_cxn]}")
                if endstop in self.used_endstop_connectors.keys() and not found_node:
                    select_new = True
                    self.write_message(
                        f"That endstop connector is already used by {self.used_endstop_connectors[endstop]}")
                if not select_new:
                    if not found_node:
                        self.conf_syr += 1
                        syringe_name = f"syringe{self.conf_syr}"
                        self.graph_tmp.add_node(syringe_name)
                    else:
                        syringe_name = self.graph_tmp.nodes[found_node]["name"]
                    node = self.graph_tmp.nodes[syringe_name]
                    node["name"] = syringe_name
                    stepper_name = f"stepper{motor_cxn}"
                    self.used_motor_connectors[motor_cxn] = syringe_name
                    self.used_endstop_connectors[endstop] = syringe_name
                    node["mod_type"] = "syringe_pump"
                    node["class_type"] = "SyringePump"
                    node["mod_config"] = {"screw_lead": 8, "linear_stepper": True, "backlash": 780}
                    node["devices"] = self.motor_setup(stepper_name, motor_cxn, config_type="default")
                    node["endstop"] = self.es_options[endstop]
                    self.read_fields(node_info, node)
                    self.add_edge(True, node["name"], valve_info["valve_name"], False,
                                  port=[valve_info["valve_id"], valve_info["port_no"]],
                                  tubing_length=0)
                    button.configure(bg="lawn green")
                    window.destroy()
                    self.config_cxn_flag = True
            else:
                if not motor_cxn:
                    self.write_message("Please select a motor connector")
                if not endstop:
                    self.write_message("Please select an endstop connector")

        label = tk.Label(window, text=f"syringe{self.conf_syr + 1}", font=self.fonts["heading"],
                         fg=self.colours["heading"])
        label.grid(row=2, column=0, columnspan=2)
        motor_connector = tk.StringVar(window)
        endstop_connector = tk.StringVar(window)

        motor_connection_label = tk.Label(window, text="Which motor connector is used for this syringe",
                                          font=self.fonts["heading"], fg=self.colours["heading"])
        motor_connection_label.grid(row=3, column=0)
        i = 4
        options = list(self.motor_options.keys())
        selected = list(self.used_motor_connectors.keys())
        for motor in options:
            tk.Radiobutton(window, text=motor, variable=motor_connector, value=motor).grid(row=i, column=0)
            i += 1
        motor_connector.set(self.find_unselected(options, selected))

        endstop_label = tk.Label(window, text="Which endstop connection is used for this syringe?",
                                 font=self.fonts["heading"], fg=self.colours["heading"])
        endstop_label.grid(row=9, column=0)
        i = 10
        options = list(self.es_options.keys())
        selected = list(self.used_endstop_connectors.keys())
        for option in options:
            tk.Radiobutton(window, text=option, variable=endstop_connector, value=option).grid(row=i, column=0)
            i += 1
        endstop_connector.set(self.find_unselected(options, selected))

        offset = i
        offset = self.generate_fields(node_info, window, fields, offset) + 1

        accept_button = tk.Button(window, text="Accept", fg="black", bg="lawn green", font=self.fonts["buttons"],
                                  command=accept)
        cancel_button = tk.Button(window, text="Cancel", fg="black", bg="tomato2", font=self.fonts["buttons"],
                                  command=window.destroy)
        accept_button.grid(row=offset, column=2)
        cancel_button.grid(row=offset, column=3)
        # if previously configured, get the old configuration for the user to update.
        if found_node:
            this_node = self.graph_tmp.nodes[found_node]
            endstop_connector.set(self.get_key(this_node["endstop"], self.es_options))
            self.update_node_entries(node_info, valve_info, this_node)
            mtr_cxn = this_node["devices"]["stepper"]["name"][-1]
            if mtr_cxn in ["0", "1"]:
                mtr_cxn = this_node["devices"]["stepper"]["name"][-2:]
            motor_connector.set(mtr_cxn)
            self.used_motor_connectors[mtr_cxn] = this_node["name"]

    def valve_setup(self, valve_info, valve_button):
        """Starts a window for the user to configure the valve. Sets up the valve using the information provided by the
        user

        Args:
            valve_info (dict): contains information about the valve
            valve_button (tk.Button): the button used to start this window
        """
        def accept(button):
            motor_cxn = motor_connector.get()
            try:
                pin = hall_connector.get()
                gear = geared_motor.get()
                hall_sensor = pins[pin]
            except KeyError:
                self.write_message("Please select a pin for the hall-effect sensor")
            else:
                if motor_cxn:
                    if motor_cxn in self.used_motor_connectors.keys() and not self.config_cxn_flag:
                        self.write_message(
                            f"That motor connector is already used by {self.used_motor_connectors[motor_cxn]}")
                    elif pin in self.used_he_pins and not self.config_cxn_flag:
                        self.write_message(
                            f"{pin} is already in use. Please select another pin")
                    else:
                        if not self.config_cxn_flag or not devices:
                            self.num_he_sens += 1
                        valve_name = valve_info["valve_name"]
                        node = self.graph_tmp.nodes[valve_name]
                        stepper_name = f"stepper{motor_cxn}"
                        he_sens_name = f"he_sens{self.num_he_sens}"
                        self.used_motor_connectors[motor_cxn] = valve_name
                        self.used_he_pins.append(pin)
                        if gear == "":
                            gear = "Direct drive"
                        node["mod_config"] = {"ports": 10, "linear_stepper": False, "gear": gear}
                        node["devices"] = {}
                        node["devices"].update(
                            self.motor_setup(stepper_name, motor_cxn, config_type="valve"))
                        node["devices"]["he_sens"] = {"name": he_sens_name, "cmd_id": hall_sensor, "device_config": {}}
                        self.cmd_devices.devices[hall_sensor] = {"command_id": hall_sensor}
                        button.configure(bg="lawn green")
                        window.destroy()
                        self.config_cxn_flag = True
                        self.conf_valves += 1

        pins = {"Analog Read 1 (A3)": "AR1", "Analog Read 2 (A4)": "AR2"}
        window = tk.Toplevel(self.primary)
        label = tk.Label(window, text=f"Valve {self.conf_valves + 1}")
        label.grid(row=2, column=0, columnspan=2)
        motor_connector = tk.StringVar(window)
        hall_connector = tk.StringVar(window)
        geared_motor = tk.StringVar(window)

        motor_connection_label = tk.Label(window, text="Which motor connector is used for this valve?",
                                          font=self.fonts["heading"])
        motor_connection_label.grid(row=3, column=0)
        i = 4
        options = list(self.motor_options.keys())
        selected = list(self.used_motor_connectors.keys())
        for motor_cn in options:
            tk.Radiobutton(window, text=motor_cn, variable=motor_connector, value=motor_cn).grid(row=i, column=0)
            i += 1
        motor_connector.set(self.find_unselected(options, selected))

        hall_sensor_label = tk.Label(window, text="Which pin is the hall sensor plugged into?",
                                     font=self.fonts["heading"])
        hall_sensor_label.grid(row=9, column=0)
        hall_options = list(pins.keys())
        hall_sensor_selector = tk.OptionMenu(window, hall_connector, *hall_options)
        hall_sensor_selector.grid(row=10, column=0)

        gear_options = ["Direct drive", "1.5:1", "2:1", "3:1"]
        geared_motor.set("")
        gear_label = tk.Label(window, text="Gear options:", font=self.fonts["heading"])
        gear_label.grid(row=12)
        gear_selector = tk.OptionMenu(window, geared_motor, *gear_options)
        gear_selector.grid(row=13)

        offset = 14
        accept_button = tk.Button(window, text="Accept", fg="black", bg="lawn green", font=self.fonts["buttons"],
                                  command=lambda: accept(valve_button))
        cancel_button = tk.Button(window, text="Cancel", fg="black", bg="tomato2", font=self.fonts["buttons"],
                                  command=window.destroy)
        accept_button.grid(row=offset + 1, column=0)
        cancel_button.grid(row=offset + 1, column=1)
        config_valve = self.graph_tmp.nodes[valve_info["valve_name"]]
        devices = config_valve.get("devices")
        # if valve has been configured already, get that information so the user can update it.
        if self.config_cxn_flag and devices is not None:
            # set the hall pin
            found_node = self.graph_tmp.nodes[valve_info["valve_name"]]
            he_cxn = self.get_key(found_node["devices"]["he_sens"]["cmd_id"], pins)
            hall_connector.set(he_cxn)
            self.used_he_pins.append(he_cxn)
            # set the motor using the stepper letter (X, Y, Z...)
            mtr_cxn = found_node["devices"]["stepper"]["name"][-1]
            if mtr_cxn in ["0", "1"]:
                mtr_cxn = found_node["devices"]["stepper"]["name"][-2:]
            motor_connector.set(mtr_cxn)
            self.used_motor_connectors[mtr_cxn] = valve_info["valve_name"]
            # set the gear
            geared_motor.set(found_node["mod_config"]["gear"])

    def storage_setup(self, node_info, valve_info, fields, window, button, found_node):
        """This window allows the user to set up a storage module. Currently, this assumes that the 
        storage unit is built like the Cronin group's clusterbot, using a single stepper motor to
        drive a Geneva wheel.

        Args:
            node_info (dict): information about the node being configured
            valve_info (dict): information about the valve this storage unit is connected to
            fields (list): list of fields that the user must fill to configure the storage unit
            window (tk.TopLevel): the window that the configuration fields are placed within
            button (tk.Button): the button used to start this window
            found_node (str): the name of the previously configured node, if found. 
        """
        def accept():
            motor_cxn = motor_connector.get()
            select_new = False
            if motor_cxn in self.used_motor_connectors.keys() and not found_node:
                select_new = True
                self.write_message(f"That motor connector is already in use by {self.used_motor_connectors[motor_cxn]}")
            if not select_new:
                self.conf_storage += 1
                storage_name = f"storage{self.conf_storage}"
                if not self.graph_tmp.nodes.get(storage_name):
                    self.graph_tmp.add_node(storage_name)
                node = self.graph_tmp.nodes[storage_name]
                stepper_name = f"stepper{motor_cxn}"
                self.used_motor_connectors[motor_cxn] = storage_name
                node["name"] = storage_name
                node["mod_type"] = "storage"
                node["class_type"] = "FluidStorage"
                node["devices"] = self.motor_setup(stepper_name, motor_cxn, config_type="default")
                node["mod_config"] = {"linear_stepper": False}
                tubing_length = self.read_fields(node_info, node)
                self.add_edge(True, node["name"], valve_info["valve_name"], found_node,
                              port=[valve_info["valve_id"], valve_info["port_no"]],
                              tubing_length=tubing_length)
                button.configure(bg="lawn green")
                window.destroy()
                self.config_cxn_flag = True

        label = tk.Label(window, text="Storage setup", font=self.fonts["heading"], fg=self.colours["heading"])
        label.grid(row=2, column=0, columnspan=2)
        motor_connector = tk.StringVar(window)
        motor_connector_label = tk.Label(window, text="Which motor connector is used for the storage?",
                                         font=self.fonts["heading"], fg=self.colours["heading"])
        motor_connector_label.grid(row=3, column=0)
        options = list(self.motor_options.keys())
        selected = list(self.used_motor_connectors.keys())
        i = 4
        for motor in options:
            tk.Radiobutton(window, text=motor, variable=motor_connector, value=motor).grid(row=i, column=0)
            i += 1
        motor_connector.set(self.find_unselected(options, selected))
        offset = i
        offset = self.generate_fields(node_info, window, fields, offset) + 1
        accept_button = tk.Button(window, text="Accept", fg="black", bg="lawn green", font=self.fonts["buttons"],
                                  command=accept)
        cancel_button = tk.Button(window, text="Cancel", fg="black", bg="tomato2", font=self.fonts["buttons"],
                                  command=window.destroy)
        accept_button.grid(row=offset, column=0)
        cancel_button.grid(row=offset, column=1)
        if found_node:
            this_node = self.graph_tmp.nodes[found_node]
            # get the stepper letter (X, Y, Z...)
            mtr_cxn = self.graph_tmp.nodes[found_node]["devices"]["stepper"]["name"][-1]
            if mtr_cxn in ["0", "1"]:
                mtr_cxn = this_node["devices"]["stepper"]["name"][-2:]
            motor_connector.set(mtr_cxn)
            self.used_motor_connectors[mtr_cxn] = this_node["name"]
            self.update_node_entries(node_info, valve_info, this_node)

    def camera_setup(self, camera_button):
        """Sets up a camera to be used with OpenCV

        Args:
            camera_button (tk.Button): the button used to start this window.
        """
        def accept():
            self.graph_tmp.add_node("camera1")
            node = self.graph_tmp.nodes["camera1"]
            node["name"] = "camera1"
            node["mod_type"] = "camera"
            node["class_type"] = "Camera"
            node["mod_config"] = {"ROI": self.roi}
            camera_button.configure(bg="lawn green")
            cap.release()
            cv.destroyAllWindows()
            window.destroy()

        def cancel():
            cap.release()
            cv.destroyAllWindows()
            window.destroy()

        def video_stream():
            _, self.frame = cap.read()
            img = cv.cvtColor(self.frame, cv.COLOR_BGR2RGBA)
            tkimg = Image.fromarray(img)
            imgtk = ImageTk.PhotoImage(image=tkimg)
            img_label.imgtk = imgtk
            img_label.configure(image=imgtk)
            img_label.after(1, video_stream)

        def setup_roi():
            warning2 = tk.Toplevel(window)
            warn_label2 = tk.Label(warning2, text="Press space or enter when done. Press c to cancel")
            warn_label2.grid()
            self.roi = cv.selectROI("Select ROI", self.frame)
            warning2.destroy()
            cv.destroyAllWindows()

        window = tk.Toplevel(self.primary)
        cap = cv.VideoCapture(0)
        label = tk.Label(window, text="Camera", font=self.fonts["heading"], fg=self.colours["heading"])
        label.grid(row=1, column=0, columnspan=2)
        label = tk.Label(window, text="Please place the camera, then use the button to set the region of interest.",
                         font=self.fonts["labels"])
        img_label = tk.Label(window)
        label.grid(row=2, column=0, columnspan=2)
        img_label.grid(row=3, column=0, columnspan=2)
        roi_butt = tk.Button(window, text="Configure ROI", font=self.fonts["buttons"], bg=self.colours["other-button"],
                             command=setup_roi)
        roi_butt.grid(row=4, column=0, columnspan=2)
        accept_butt = tk.Button(window, text="Accept", font=self.fonts["buttons"], bg=self.colours["accept-button"],
                                command=accept)
        cancel_butt = tk.Button(window, text="Cancel", font=self.fonts["buttons"], bg=self.colours["cancel-button"],
                                command=cancel)
        accept_butt.grid(row=5, column=1)
        cancel_butt.grid(row=5, column=3)
        video_stream()

    def valve_link(self, node_info, valve_info, fields, window, button, found_node):
        """Set up an edge between two valves

        Args:
            node_info (dict): contains known information about the node
            valve_info (dict): contains known information about the valve
            fields (list): the fields to create for this form
            found_node (str): whether a previously configured node has been found
            window (tk.TopLevel): this window
            button (tk.Button): The button to colour once this method is run
        """

        def accept_valve_link(sel_valve, tube_length, valve_button):
            valve_name = sel_valve.get()
            if valve_name != "":
                valve = self.graph_tmp.nodes[valve_name]
                self.used_valves.append(valve_name)
                node = {"mod_config": {}}
                if tube_length == 0:
                    tube_length = self.read_fields(node_info, node)
                self.add_edge(True, valve["name"], valve_info["valve_name"], found_node,
                              port=[valve_info["valve_id"], valve_info["port_no"]],
                              tubing_length=tube_length)
                valve_button.configure(bg="lawn green")
                window.destroy()
                self.config_cxn_flag = True
            else:
                self.write_message("Please select a valve")

        tubing_length = 0
        possible_valves = [m for m in self.graph_tmp.nodes.keys() if "valve" in m]
        selected_valve = tk.StringVar(window)
        selector_label = tk.Label(window, text=f"Which valve is {valve_info['valve_name']} connected to:")
        valve_selector = tk.OptionMenu(window, selected_valve, *possible_valves)
        selected_valve.set(self.find_unselected(possible_valves, self.used_valves))
        selector_label.grid()
        offset = self.generate_fields(node_info, window, fields, 1) + 1
        valve_selector.grid(row=offset + 1, column=1)
        if found_node:
            selected_valve.set(found_node)
            tubing_length = self.graph_tmp.adj[valve_info["valve_name"]][found_node][0]["tubing_length"]
            self.update_node_entries(node_info, valve_info, self.graph_tmp.nodes[found_node])
        valve_ok = tk.Button(window, text="Accept", fg="black", bg="lawn green", font=self.fonts["buttons"],
                             command=lambda sel_valve=selected_valve, tube_len=tubing_length: accept_valve_link(
                                 sel_valve, tube_len, button))
        cancel_butt = tk.Button(window, text="Cancel", fg="black", font=self.fonts["buttons"],
                                bg="tomato2", command=window.destroy)
        valve_ok.grid(row=offset + 2, column=1)
        cancel_butt.grid(row=offset + 2, column=2)

    def motor_setup(self, stepper_name, motor_cn, config_type):
        """Setups up the dictionary structure required for the robot to set up the stepper motors

        Args:
            stepper_name (str): the name of the stepper motor, e.g. stepperX
            motor_cn (str): the stepper driver that the motor is connected to. On RAMPS 1.4 these are marked on the
            silkscreen
            config_type (str): the type of configuration to apply for the motor

        Returns:
            dict: the dictionary describing the motor's configuration.
        """
        this_motor_config = {"name": stepper_name}
        motor_options = self.motor_options[motor_cn][stepper_name]
        motor_options["device_config"].update(self.motor_configs[config_type])
        this_motor_config.update(motor_options)
        return {"stepper": this_motor_config}

    def flask_setup(self, node_info, valve_info, fields, window, button, found_node):
        """Sets up a flask (any vessel for holding fluid)

        Args:
            node_info (dict): known information about the node/module
            valve_info (dict): information about the valve this flask is connected to
            fields (list): the fields the user should complete to configure this flask
            window (tk.TopLevel): this window
            button (tk.Button): the button used to start this window
            found_node (str): the name of the previously configured node, if found. 
        """
        def accept_flask(flask_button):
            if not found_node:
                flask_name = f"flask{valve_info['valve_id']}{valve_info['port_no']}"
            else:
                flask_name = self.graph_tmp.nodes[found_node]
            self.graph_tmp.add_node(flask_name)
            node = self.graph_tmp.nodes[flask_name]
            node["name"] = flask_name
            node["mod_config"] = {}
            node["mod_type"] = "flask"
            tubing_length = self.read_fields(node_info, node)
            if "waste" in node["mod_config"]["contents"].lower():
                node["mod_type"] = "waste"
                node["mod_config"]["contents"] = "waste"
            self.add_edge(True, node["name"], valve_info["valve_name"], found_node,
                          port=[valve_info["valve_id"], valve_info["port_no"]],
                          tubing_length=tubing_length)
            self.num_flasks += 1
            flask_button.configure(bg="lawn green")
            window.destroy()
            self.config_cxn_flag = True

        offset = self.generate_fields(node_info, window, fields, 2) + 1
        flask_ok = tk.Button(window, text="Accept", fg="black", bg="lawn green", font=self.fonts["buttons"],
                             command=lambda: accept_flask(button))
        flask_cancel = tk.Button(window, text="Cancel", fg="black", bg="tomato2", font=self.fonts["buttons"],
                                 command=window.destroy)
        flask_ok.grid(row=offset, column=1)
        flask_cancel.grid(row=offset, column=2)
        if found_node:
            this_node = self.graph_tmp.nodes[found_node]
            self.update_node_entries(node_info, valve_info, this_node)

    def reactor_setup(self, node_info, valve_info, fields, window, button, found_node):
        """This window allows the user to set up a reactor (stirrer hotplate)

        Args:
            node_info (dict): known information about the node/module
            valve_info (dict): information about the valve this module is connected to
            fields (list): the fields required to configure this module
            window (tk.TopLevel): this window
            button (tk.Button): the button used to start this window.
            found_node (str): the name of the previously configured node, if found.
        """
        def accept_reactor(reactor_button):
            try:
                stirrer = stir_pin.get()
                heater = heat_pin.get()
                thermistor = temp_pin.get()
                stirrer = pins[stirrer]
                heater = pins[heater]
            except KeyError:
                self.write_message("Please select pins for the reactor devices")
            else:
                if not found_node:
                    reactor_name = f"reactor{self.num_reactors}"
                else:
                    reactor_name = self.graph_tmp.nodes[found_node]
                self.graph_tmp.add_node(reactor_name)
                node = self.graph_tmp.nodes[reactor_name]
                node["name"] = reactor_name
                node["mod_config"] = {}
                node["mod_type"] = "reactor"
                tubing_length = self.read_fields(node_info, node)
                node["devices"] = {"heater": {"name": "heater1", "cmd_id": heater, "device_config": {}},
                                   "mag_stirrer": {"name": "stirrer1", "cmd_id": stirrer,
                                                   "device_config": {"fan_speed": node["mod_config"]["fan_speed"]}},
                                   "temp_sensor": {"name": "temp_sensor1", "cmd_id": thermistor,
                                                   "device_config": {"SH_C": [0.0008271125019925238,
                                                                              0.0002088017729221142,
                                                                              8.059262669466295e-08]}}}
                self.add_edge(True, node["name"], valve_info["valve_name"], found_node,
                              port=[valve_info["valve_id"], valve_info["port_no"]],
                              tubing_length=tubing_length)
                self.cmd_devices.devices[thermistor] = {"command_id": thermistor}
                self.cmd_devices.devices[stirrer] = {"command_id": stirrer}
                self.cmd_devices.devices[heater] = {"command_id": heater}
                reactor_button.configure(bg="lawn green")
                window.destroy()
                self.config_cxn_flag = True

        pins = {"D8": "AW1", "D9": "AW2", "D10": "AW3"}
        temp_pins = ["T1", "T2"]
        heat_pin = tk.StringVar()
        stir_pin = tk.StringVar()
        temp_pin = tk.StringVar()

        offset = self.generate_fields(node_info, window, fields, 2) + 1
        pin_heat_label = tk.Label(window, text="Which pin is the heater connected to?")
        pin_heat_selector = tk.OptionMenu(window, heat_pin, *list(pins.keys()))
        pin_heat_label.grid(row=offset)
        pin_heat_selector.grid(row=offset, column=1)

        pin_stir_label = tk.Label(window, text="Which pin is the stirrer connected to?")
        pin_stir_label.grid(row=offset + 1)
        pin_stir_selector = tk.OptionMenu(window, stir_pin, *list(pins.keys()))
        pin_stir_selector.grid(row=offset + 1, column=1)

        tpin_label = tk.Label(window, text="Which pin is the thermistor attached to?")
        tpin_label.grid(row=offset + 2)
        tpin_selector = tk.OptionMenu(window, temp_pin, *temp_pins)
        tpin_selector.grid(row=offset + 2, column=1)

        reactor_ok = tk.Button(window, text="Accept", fg="black", bg="lawn green", font=self.fonts["buttons"],
                               command=lambda: accept_reactor(button))
        reactor_ok.grid(row=offset + 3)
        reactor_cancel = tk.Button(window, text="Cancel", fg="black", font=self.fonts["buttons"],
                                   bg="tomato2", command=window.destroy)
        reactor_cancel.grid(row=offset + 3, column=2)
        if found_node:
            this_node = self.graph_tmp.nodes[found_node]
            heat_pin.set(self.get_key(this_node["devices"]["heater"]["cmd_id"], pins))
            temp_pin.set(this_node["devices"]["temp_sensor"]["cmd_id"])
            stir_pin.set(self.get_key(this_node["devices"]["mag_stirrer"]["cmd_id"], pins))
            self.update_node_entries(node_info, valve_info, this_node)

    def validate_text(self, new_text):
        """Validates whether the text can be converted to a string

        Args:
            new_text (str): the input to the field.

        Returns:
            bool: whether the input could be successfully converted to str.
        """
        if not new_text:
            self.text_temp = ""
            return True
        try:
            self.text_temp = str(new_text)
            return True
        except ValueError:
            return False

    def validate_int(self, new_int):
        """Validates whether the text can be converted to an integer

        Args:
            new_int (str): the input to the field.

        Returns:
            bool: whether the input could be successfully converted to int.
        """
        if not new_int:
            self.int_temp = 0
            return True
        try:
            self.int_temp = int(new_int)
            return True
        except ValueError:
            return False

    @staticmethod
    def get_key(value, search_dict):
        """Gets the key corresponding to a dictionary value. 

        Args:
            value (str): the value of the dictionary item
            search_dict (dict): the ditionary to search

        Returns:
            str: the key corresponding to value
        """
        for k, v in search_dict.items():
            if v == value:
                return k

    def update_node_entries(self, node_info, valve_info, node):
        """Fills the entry fields using information from the node that has already been configured.

        Args:
            node_info (dict): contains the entries and other information about the node
            valve_info (dict): contains information about the valve this module is connected to.
            node (dict): the dictionary corresponding to this node on the graph
        """
        for f in node_info["entries"]:
            if f[0] == "Tubing length in mm":
                edges = self.graph_tmp.adj[node["name"]][valve_info["valve_name"]]
                tubing_length = edges[0]["tubing_length"]
                f[1].insert(0, tubing_length)
            else:
                text = node["mod_config"].get(FIELD_NAMES.get(f[0], f[0]))
                f[1].insert(0, text)

    @staticmethod
    def find_unselected(possible_options, selected_options):
        """Finds an unselected option in a menu

        Args:
            possible_options (list): all possible options
            selected_options (list): options that have been selected

        Returns:
            str: an option that has not been selected
        """
        options = list(possible_options)
        selected = list(selected_options)
        for option in options:
            if option not in selected:
                return option

    @staticmethod
    def generate_fields(node_info, frame, field_list, offset):
        """Generates input fields for the configuration windows.

        Args:
            node_info (dict): known information about the node being configured
            frame (tk.Frame): the frame that the fields are being added to
            field_list (list): list of the fields that must be added
            offset (int): the row offset to apply

        Returns:
            int: the new row offset
        """
        # todo add validation to volume entries
        index = 0
        for index, field in enumerate(field_list):
            label = tk.Label(frame, text=field)
            label.grid(row=index + offset, column=0)
            entry = tk.Entry(frame)
            entry.grid(row=index + offset, column=1)
            node_info["entries"].append((field, entry))
        return index + offset

    @staticmethod
    def read_fields(node_info, node, start_field=0):
        """Reads the fields filled in by the user

        Args:
            node_info (dict): dictionary containing known information and the entry objects
            node (dict): dictionary corresponding to this node in the graph
            start_field (int, optional): the field to start reading from. Defaults to 0.

        Returns:
            float: the length of the tubing (if applicable)
        """
        entries = node_info["entries"]
        tubing_length = 0
        for i in range(start_field, len(entries)):
            field = entries[i][0]
            if field == "Tubing length in mm":
                try:
                    tubing_length = float(entries[i][1].get())
                except ValueError:
                    tubing_length = 0
            else:
                config = entries[i][1].get()
                field = FIELD_NAMES.get(field, field)
                units = UNITS.get(field)
                if units is None:
                    config = str(config)
                elif units == "float":
                    config = float(config)
                elif units == "int":
                    config = int(config)
                node["mod_config"].update([(field, config)])
        return tubing_length

    def get_node(self, valve_name, port):
        """Determines whether a node has already configured for this port

        Args:
            valve_name (str): the name of the valve this node is connected to
            port (int): the port number for this node

        Returns:
            str: the name of the node, if found
        """
        adj_nodes = self.graph_tmp.adj[valve_name]
        for node in adj_nodes:
            for edge in adj_nodes[node]:
                if adj_nodes[node][edge]["port"][1] == port:
                    return node
        return ""

    @staticmethod
    def delete_fields(o_frame):
        for widget in o_frame.winfo_children():
            widget.destroy()

    def add_edge(self, dual, *args, **kwargs):
        """Adds edges between configured nodes

        Args:
            dual (bool): whether the edge is multidirectional or not
        """
        if args[2]:
            try:
                self.graph_tmp.adj[args[0]][args[1]][0]["tubing_length"] = kwargs["tubing_length"]
            except KeyError:
                self.write_message(f"{args[2]} not found in graph")
        else:
            self.graph_tmp.add_edge(args[0], args[1], **kwargs)
            if dual:
                self.graph_tmp.add_edge(args[1], args[0], **kwargs)

    def run_fb_menu(self):
        """Starts the fluidic backbone GUI as a subprocess
        """
        run_popup = tk.Toplevel(self.primary)
        run_popup.title("Run Fluidic Backbone")
        warning_label = tk.Label(run_popup,
                                 text="Have you finished configuring the system? Selecting yes will use configuration "
                                      "stored in configs folder.",
                                 font=self.fonts["text"])
        yes_button = tk.Button(run_popup, text="Yes", font=self.fonts["buttons"], bg="teal", fg="white",
                               command=self.start_fb)
        no_button = tk.Button(run_popup, text="Cancel", font=self.fonts["buttons"], bg="tomato2", fg="white",
                              command=run_popup.destroy)
        warning_label.grid(row=0, column=0)
        yes_button.grid(row=1, column=1)
        no_button.grid(row=1, column=2)

    def generate_config(self):
        """Generates the JSON configuration files. Saved to the package installation location.
        """
        if not self.cmd_devices.ios:
            self.write_message("Please configure a COM port")
            return
        config_files = []
        for filename in self.config_filenames[:2]:
            fn = os.path.join(self.script_dir, self.default_configs[3] + filename)
            config_files.append(open(fn, "w"))
        # only write running config if it doesn't already exist.
        running_config_path = os.path.join(self.script_dir, self.default_configs[3] + self.config_filenames[2])
        if not os.path.exists(running_config_path):
            with open(running_config_path, "w") as running_config:
                default_running_config = json.dumps(self.default_running_config, indent=4)
                running_config.write(default_running_config)
        # write cmd_config
        cmd_config = json.dumps(self.cmd_devices.as_dict(), indent=4)
        config_files[0].write(cmd_config)
        # write module_connections
        self.graph.add_node("meta", robot_id=self.id, key=self.key, rxn_name=self.rxn_name)
        graph_data = nx.readwrite.json_graph.node_link.node_link_data(self.graph)
        module_connections = json.dumps(graph_data, indent=4)
        config_files[1].write(module_connections)
        for file in config_files:
            file.close()
        self.write_message(f"Config files written to {self.script_dir}/configs")

    def load_configs(self, default=3):
        """Loads a previously configured JSON file.
        """
        self.clear_configs()
        cmd_config = os.path.join(self.script_dir, self.default_configs[default] + self.config_filenames[0])
        cxn_config = os.path.join(self.script_dir, self.default_configs[default] + self.config_filenames[1])
        if self.config_cmd_flag:
            self.write_message("The command configuration has already been loaded")
        else:
            self.config_cmd_flag = True
            self.cmd_devices = CmdConfig()
            try:
                with open(cmd_config) as file:
                    config = json.load(file)
                self.cmd_devices.load_existing(**config)
                self.write_message("Successfully loaded Commanduino configuration")
            except FileNotFoundError:
                self.write_message(f"File {cmd_config} not found")
        if self.config_cxn_flag:
            self.write_message("The connections configuration has already been loaded")
        else:
            self.num_he_sens, self.num_syringes, self.num_valves = 0, 0, 0
            self.used_motor_connectors = {}
            self.used_endstop_connectors = {}
            self.config_cxn_flag = True
            try:
                with open(cxn_config) as file:
                    config = json.load(file)
                self.graph = nx.readwrite.json_graph.node_link_graph(config)
                self.graph_tmp = self.graph
                for node in self.graph.nodes.keys():
                    if "valve" in node:
                        self.num_valves += 1
                        self.conf_valves += 1
                        self.num_he_sens += 1
                    elif "syringe" in node:
                        self.num_syringes += 1
                        self.conf_syr += 1
                    elif "reactor" in node:
                        self.num_reactors += 1
                    elif "flask" in node:
                        self.num_flasks += 1
                self.write_message("Successfully loaded connections configuration")
            except FileNotFoundError:
                self.write_message(f"File {self.config_filenames[1]} not found")

    def load_default_config(self):
        def accept(default_num):
            default_query.destroy()
            self.load_configs(default_num)

        default_query = tk.Toplevel(self.primary)
        default_query.attributes("-topmost", "true")
        label = tk.Label(default_query, text="Load default configurations", font=self.fonts["heading"],
                         fg=self.colours["heading"])
        b1 = tk.Button(default_query, text="1 valve, 1 syringe", fg="black", bg="lawn green",
                       command=lambda: accept(0))
        b2 = tk.Button(default_query, text="1 valve, 1 syringe, 1 reactor", fg="black", bg="lawn green",
                       command=lambda: accept(1))
        b3 = tk.Button(default_query, text="2 valves, 2 syringes, 1 reactor", fg="black", bg="lawn green",
                       command=lambda: accept(2))
        cancel_button = tk.Button(default_query, text="Cancel", fg="black", bg="tomato2", font=self.fonts["buttons"],
                                  command=default_query.destroy)
        label.grid(row=0, column=0)
        b1.grid(row=1, column=0)
        b2.grid(row=2, column=0)
        b3.grid(row=3, column=0)
        cancel_button.grid(row=4, column=1)

    def clear_configs(self):
        self.graph = nx.MultiGraph()
        self.graph_tmp = nx.MultiGraph()
        self.cmd_devices = CmdConfig()
        self.used_motor_connectors = {}
        self.used_endstop_connectors = {}
        self.num_valves = 0
        self.num_syringes = 0
        self.num_flasks = 0
        self.num_reactors = 0
        self.config_cmd_flag = False
        self.config_cxn_flag = False

    def write_message(self, message):
        """Writes a message to the log window

        Args:
            message (str): the message to be output
        """
        numlines = int(self.log.index("end - 1 line").split(".")[0])
        self.log["state"] = "normal"
        if numlines == 16:
            self.log.delete(1.0, 2.0)
        if self.log.index("end-1c") != "1.0":
            self.log.insert("end", "\n")
        lines = len(message)//79
        if lines >= 1:
            i = 0
            for i in range(lines):
                self.log.insert("end", message[i*79:(i+1)*79])
                self.log.insert("end", "\n")
            self.log.insert("end", message[(i+1)*79:])
        else:
            self.log.insert("end", message)
        self.log["state"] = "disabled"

    def start_fb(self):
        self.primary.destroy()
        directory = os.path.join(self.script_dir, "..")
        os.chdir(directory)
        subprocess.run(["python", "main.py"], shell=True)


if __name__ == "__main__":
    start_gui()
